kicksat/Mechanical/Avionics/Antenna Splitter/Antenna Splitter Assembly.SLDASM

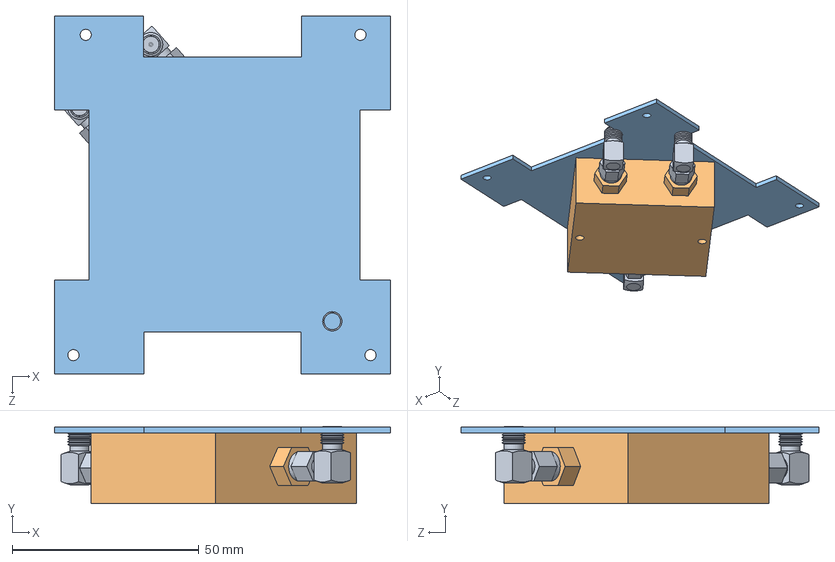
[picture p1: CAD file, 2018-08-01]
Avionics/Antenna Splitter/Antenna Splitter Assembly.SLDASM
90.0 x 20.7 x 95.9 mm
Antenna Splitter Holder
Antenna Splitter
SMA Right Angle x 3
