kicksat/Mechanical/Mechanical & Structural Components/Sprite Housing/Sprite Deployer.SLDASM

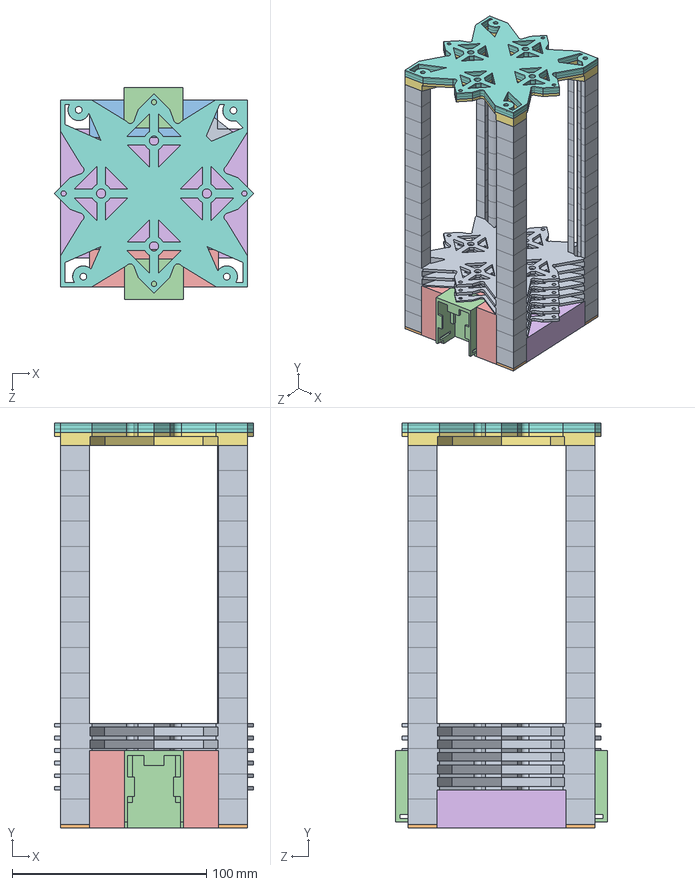
[picture p16: CAD file, 2016-09-20]
Mechanical & Structural Components/Sprite Housing/Sprite Deployer.SLDASM
102.6 x 208.4 x 109.2 mm
3dppart2 x 15
3dprintpart
BottomAntennaAttach1
Base x 2
BottomAntennaAttach2
GPSHolder
Deployer Top Part
Deployer Top Part 2 x 3
