kicksat/Mechanical/Avionics/Main Antenna/Antenna Assembly.SLDASM

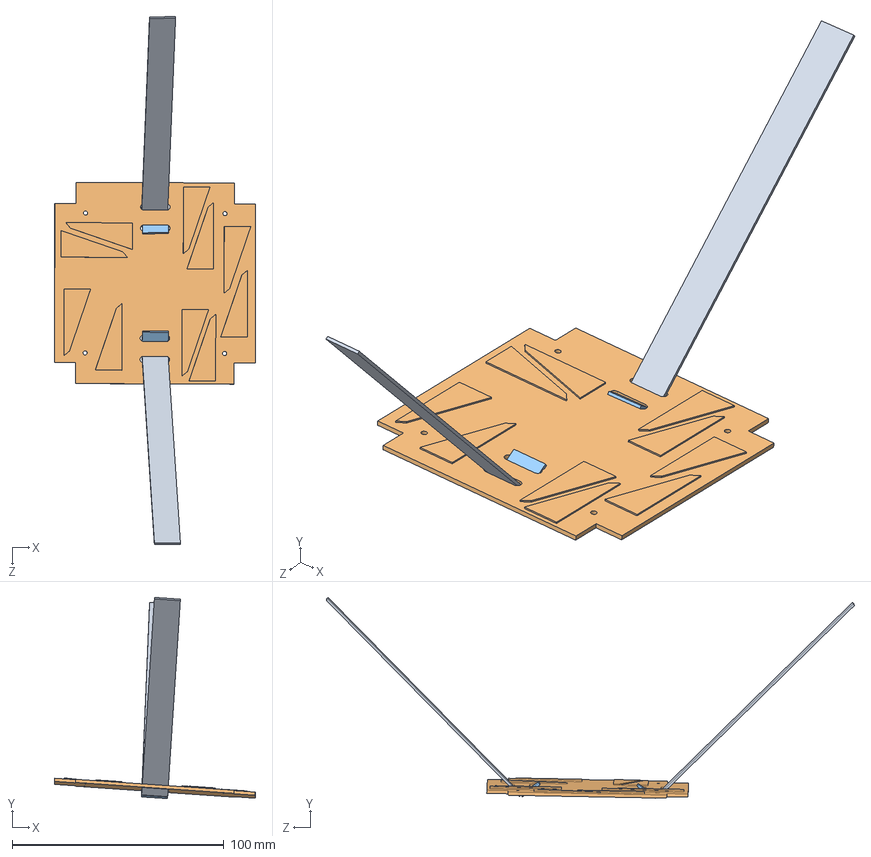
[picture p17: CAD file, 2018-08-01]
Avionics/Main Antenna/Antenna Assembly.SLDASM
95.1 x 95.0 x 249.2 mm
Antenna_Main x 2
Antenna Board
Antenna_Short x 2
