kicksat/Mechanical/Mechanical & Structural Components/Updated Deployer/UpdatedDeployerAssemblyV2.SLDASM

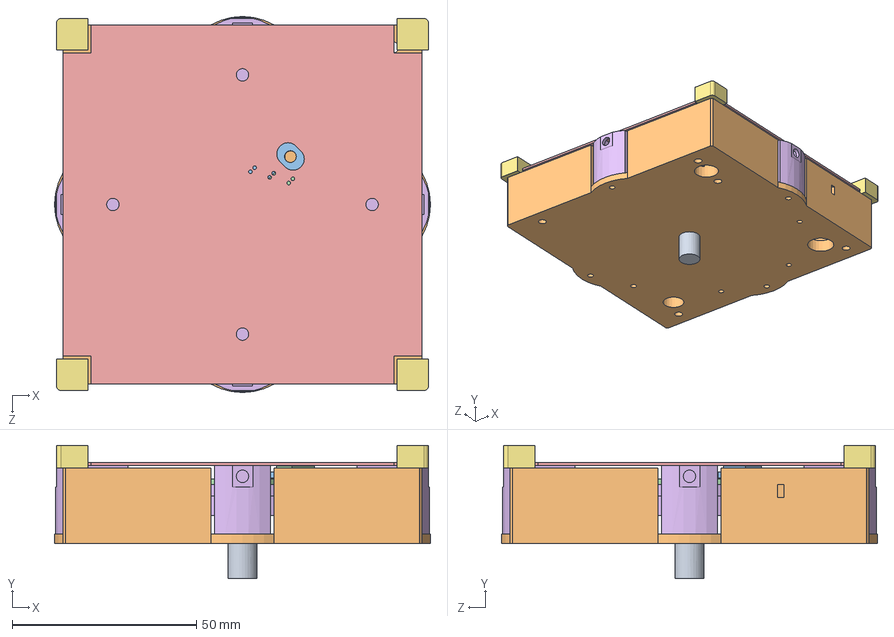
[picture p18: CAD file, 2018-09-04]
Mechanical & Structural Components/Updated Deployer/UpdatedDeployerAssemblyV2.SLDASM
102.1 x 36.2 x 102.1 mm
Bolt,8mm_x_24.6mm
DeployerBase
TopClasp
BottomClasp
CoverPlate
RetentionPlate
