kicksat/Mechanical/Mechanical & Structural Components/Sprite Deployer/Sprite Deployer.SLDASM

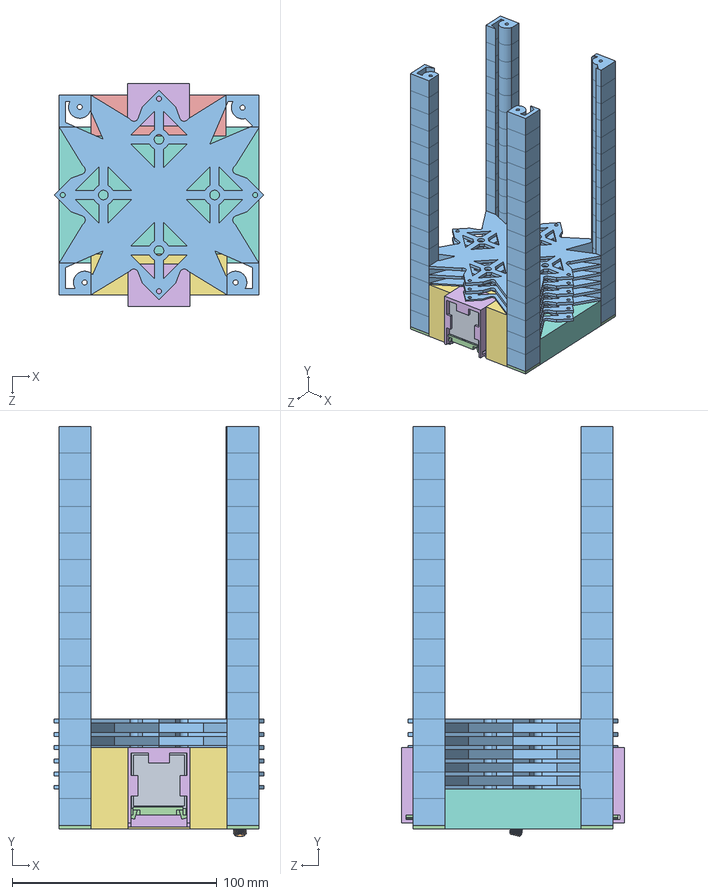
[picture p19: CAD file, 2018-08-01]
Mechanical & Structural Components/Sprite Deployer/Sprite Deployer.SLDASM
102.6 x 200.5 x 109.2 mm
3dppart2 x 15
3dprintpart
BottomAntennaAttach1
Base x 2
BottomAntennaAttach2
GPSHolder
PCB
molex 53261 x 3
FTSH-50-D
T-1S15 x 10
Micro USB
Can BMI-S-208-F
Lid BMI-S-208-F
Patch Ant GP.1575.25.4.A.02
Molex SMA 73251-1150
Led 0603 x 2
Button B3U-1000P
SMA Right Angle
GPS Antenna x 2
Slider x 2
