kicksat/Mechanical/Avionics/Batteries/M101 Battery Assembly.SLDASM

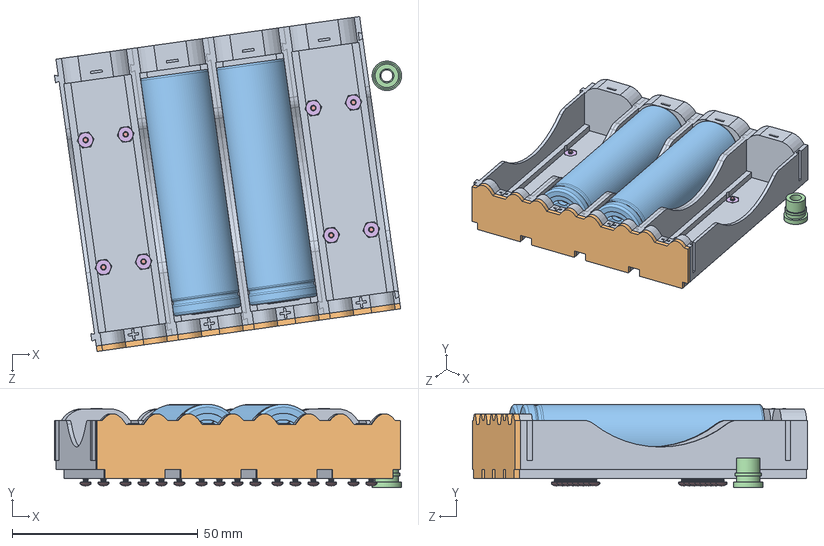
[picture p20: CAD file, 2018-08-30]
Avionics/Batteries/M101 Battery Assembly.SLDASM
93.5 x 22.5 x 90.2 mm
single battery holder x 4
battery pack cap
Battery, 18650_LGABC11865_3.7V x 2
grommet, 1-8in ID, 5269T211
screw, pan head, 0-80, 1_8L, 316SS, 91400A030 x 16
nut, 0-80, standard, 18-8SS, 91841A115 x 16
