kicksat/Mechanical/Mechanical & Structural Components/Sprite Deployer/BottomStart.SLDASM

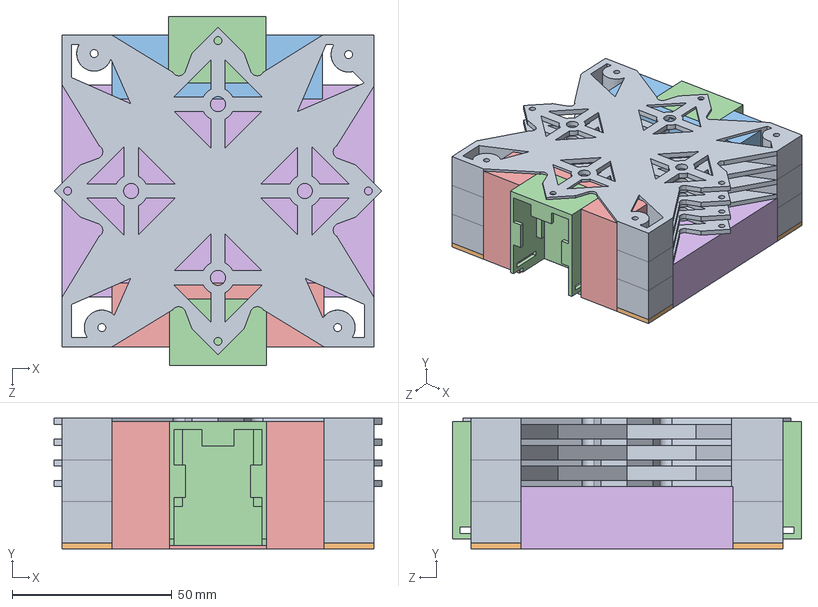
[picture p21: CAD file, 2018-08-01]
Mechanical & Structural Components/Sprite Deployer/BottomStart.SLDASM
102.6 x 40.9 x 109.2 mm
3dppart2 x 3
3dprintpart
BottomAntennaAttach1
Base x 2
BottomAntennaAttach2
GPSHolder
