kicksat/Mechanical/Avionics/GPS/piksi_v2_3_cad/FTSH-105-01-X-D-K.SLDASM

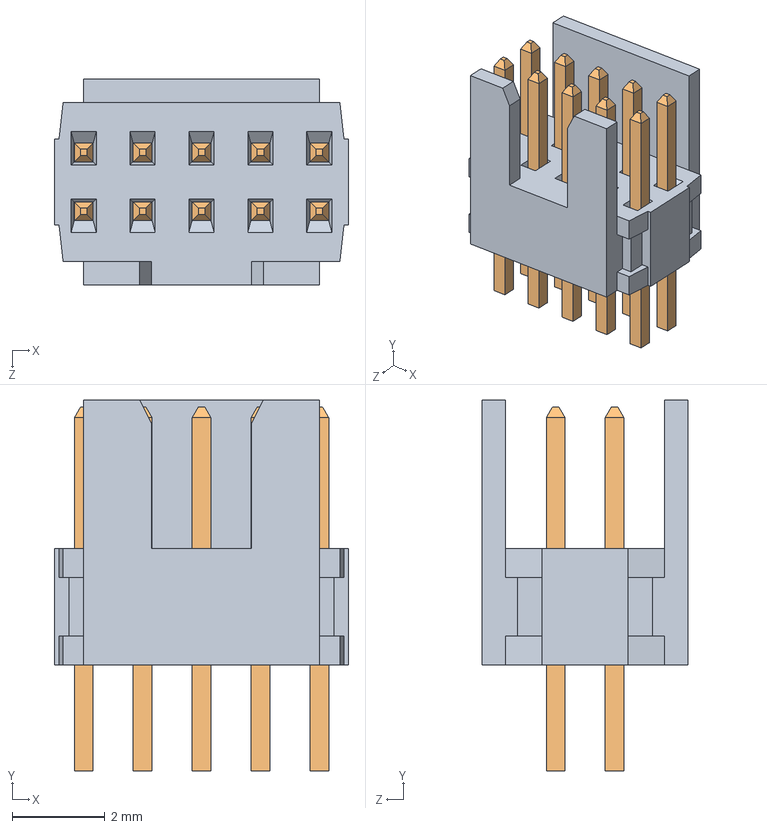
[picture p23: CAD file, 2018-08-01]
Avionics/GPS/piksi_v2_3_cad/FTSH-105-01-X-D-K.SLDASM
6.35 x 8.00 x 4.45 mm
FTSH-50-D
T-1S15 x 10
