kicksat/Mechanical/Avionics/GPS/piksi_v2_3_cad/BMI-S-208-F.SLDASM

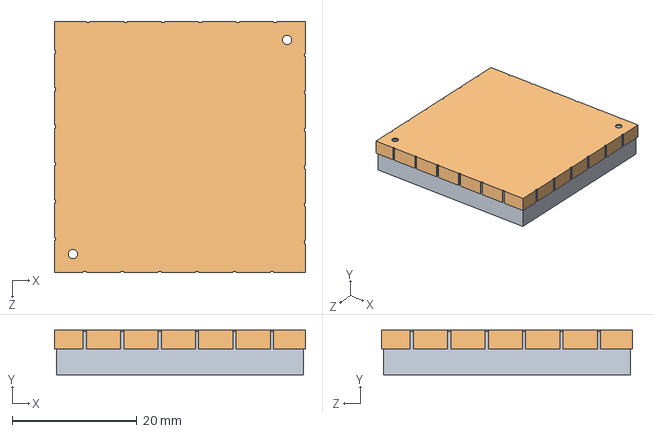
[picture p24: CAD file, 2018-08-01]
Avionics/GPS/piksi_v2_3_cad/BMI-S-208-F.SLDASM
40.2 x 7.20 x 40.2 mm
Can BMI-S-208-F
Lid BMI-S-208-F
