kicksat/Mechanical/Avionics/GPS/piksi_v2_3_cad/swiftnav_v2_3.SLDASM

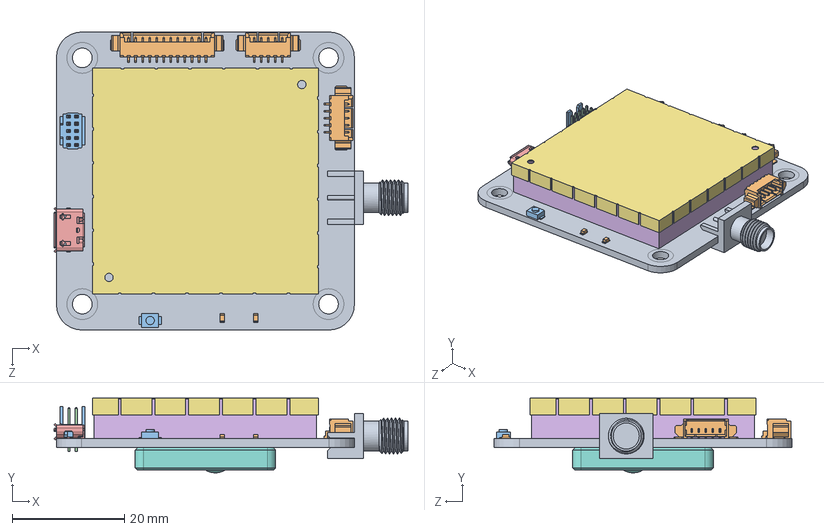
[picture p25: CAD file, 2015-09-18]
Avionics/GPS/piksi_v2_3_cad/swiftnav_v2_3.SLDASM
63.0 x 13.3 x 53.0 mm
PCB
molex 53261 x 3
FTSH-50-D
T-1S15 x 10
Micro USB
Can BMI-S-208-F
Lid BMI-S-208-F
Patch Ant GP.1575.25.4.A.02
Molex SMA 73251-1150
Led 0603 x 2
Button B3U-1000P
