kicksat/Mechanical/Avionics/Batteries/grommet, 1-8in ID, 5269T211.SLDPRT

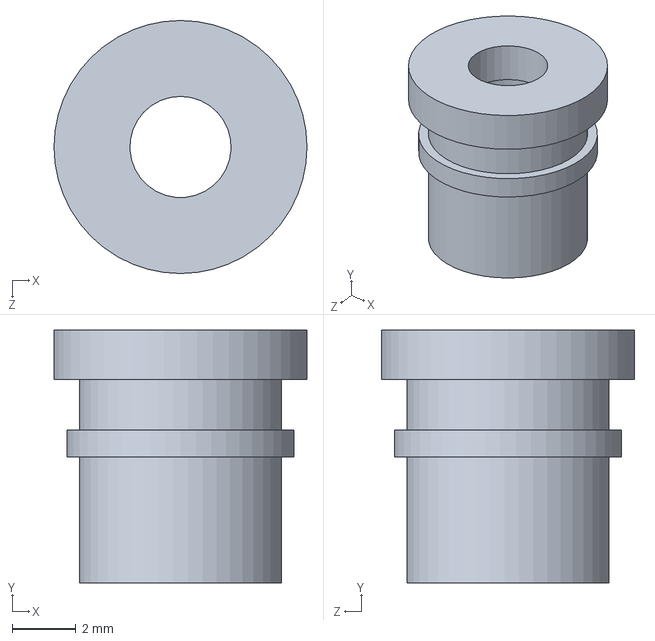
[picture p26: CAD file, 2018-08-30]
Avionics/Batteries/grommet, 1-8in ID, 5269T211.SLDPRT
7.94 x 7.94 x 7.94 mm
