kicksat/Mechanical/Avionics/Flight Computer and Radio Board/Connector1.SLDPRT

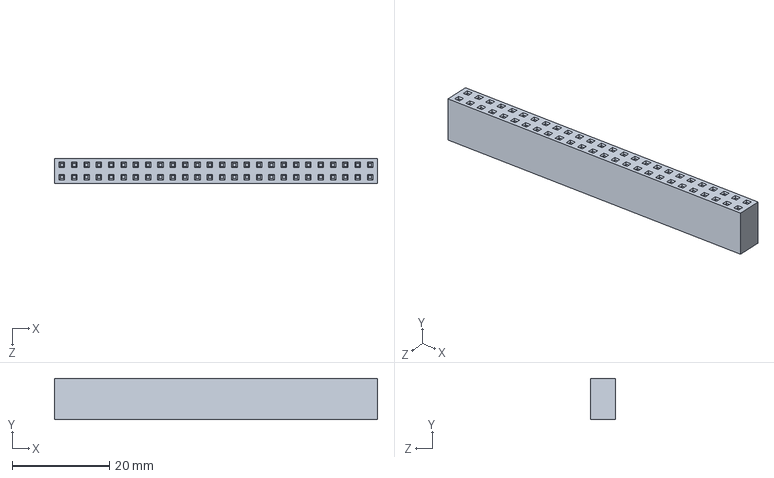
[picture p27: CAD file, 2018-08-01]
Avionics/Flight Computer and Radio Board/Connector1.SLDPRT
66.5 x 8.51 x 5.08 mm
