kicksat/Mechanical/Avionics/GPS/GPS Antenna.SLDPRT

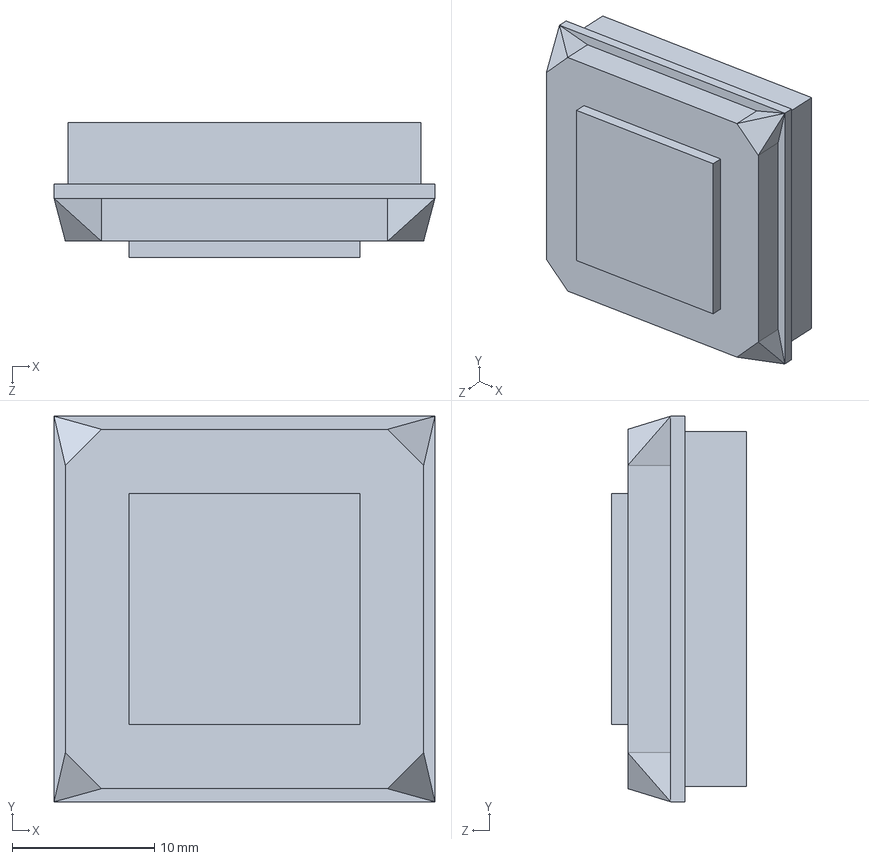
[picture p28: CAD file, 2018-08-01]
Avionics/GPS/GPS Antenna.SLDPRT
26.8 x 27.2 x 9.50 mm
