kicksat/Mechanical/Avionics/GPS/piksi_v2_3_cad/molex 53261.SLDPRT

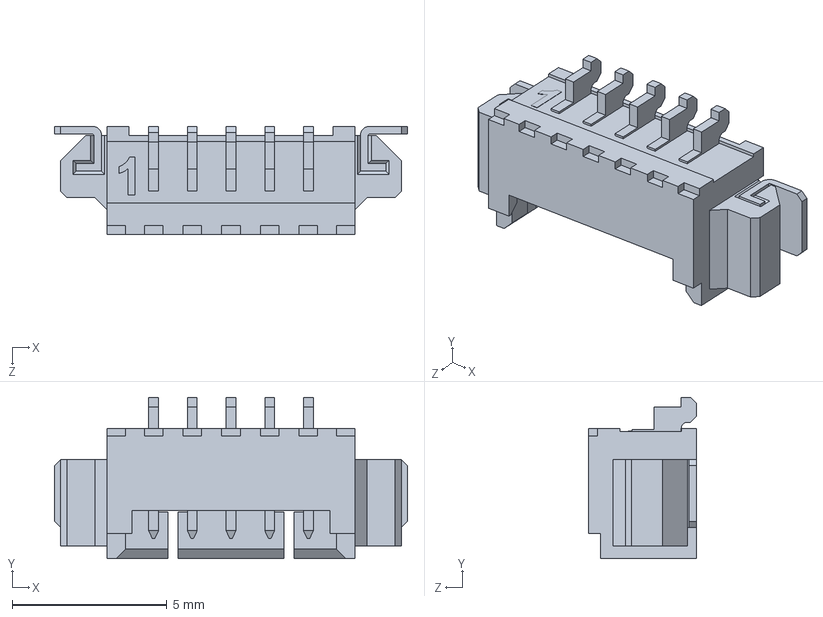
[picture p29: CAD file, 2018-08-01]
Avionics/GPS/piksi_v2_3_cad/molex 53261.SLDPRT
11.4 x 5.20 x 3.50 mm
