kicksat/Mechanical/Avionics/Main Antenna/Antenna Board.SLDPRT

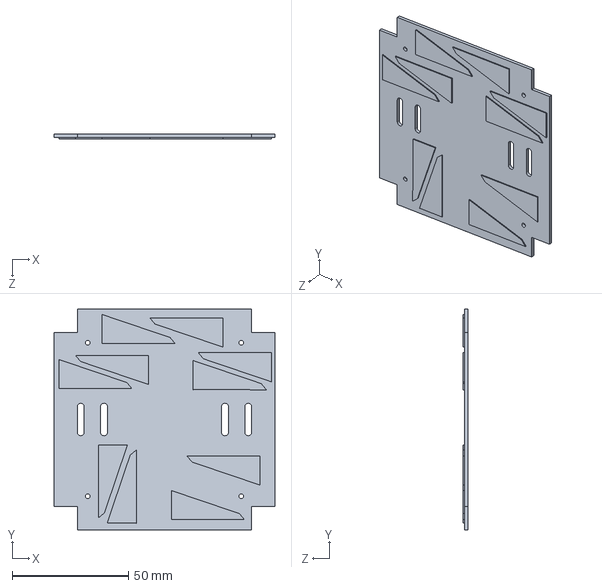
[picture p30: CAD file, 2018-08-01]
Avionics/Main Antenna/Antenna Board.SLDPRT
95.0 x 95.0 x 2.00 mm
