kicksat/Mechanical/Avionics/Polarized Connectors.SLDPRT

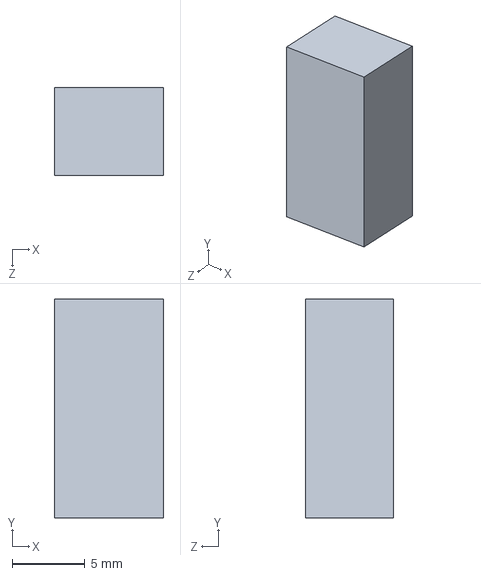
[picture p31: CAD file, 2015-09-25]
Avionics/Polarized Connectors.SLDPRT
7.50 x 15.0 x 6.00 mm
