kicksat/Mechanical/Mechanical & Structural Components/Outershell/Outershell.SLDPRT

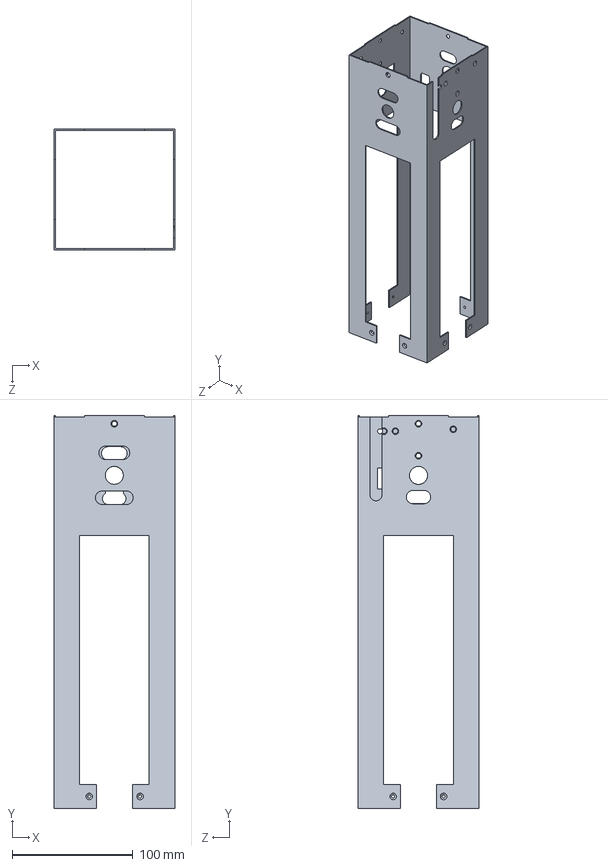
[picture p32: CAD file, 2018-08-01]
Mechanical & Structural Components/Outershell/Outershell.SLDPRT
100.0 x 325.3 x 100.0 mm
