kicksat/Mechanical/Mechanical & Structural Components/Sprite Housing/Slider.SLDPRT

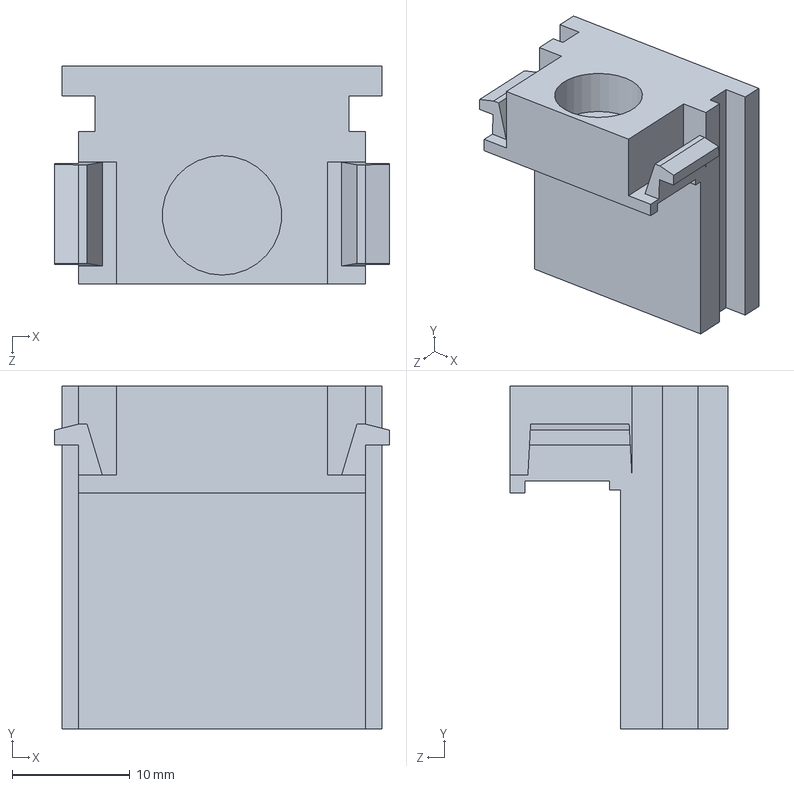
[picture p33: CAD file, 2016-11-20]
Mechanical & Structural Components/Sprite Housing/Slider.SLDPRT
28.5 x 29.1 x 18.5 mm
