kicksat/Mechanical/Mechanical & Structural Components/Top and Deployer/CarbonFiberRodX.SLDPRT

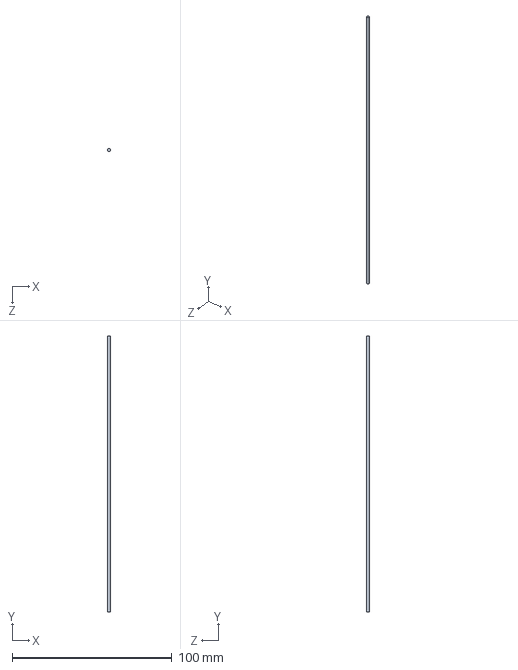
[picture p34: CAD file, 2018-08-01]
Mechanical & Structural Components/Top and Deployer/CarbonFiberRodX.SLDPRT
1.90 x 173.0 x 1.90 mm
