kicksat/Mechanical/Mechanical & Structural Components/Top and Deployer/mnc27/DeployerPiece#1_v5.STL

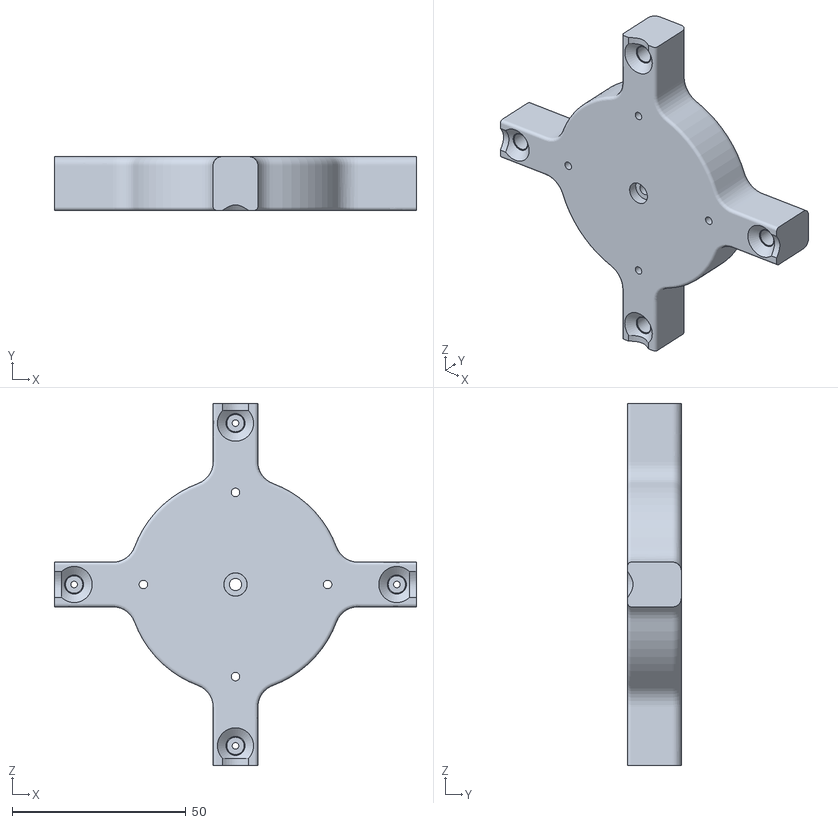
[picture p35: CAD file, 2016-10-16]
Mechanical & Structural Components/Top and Deployer/mnc27/DeployerPiece#1_v5.STL
104.2 x 15.4 x 104.2
