kicksat/Mechanical/Mechanical & Structural Components/Updated Deployer/Body1.sldprt

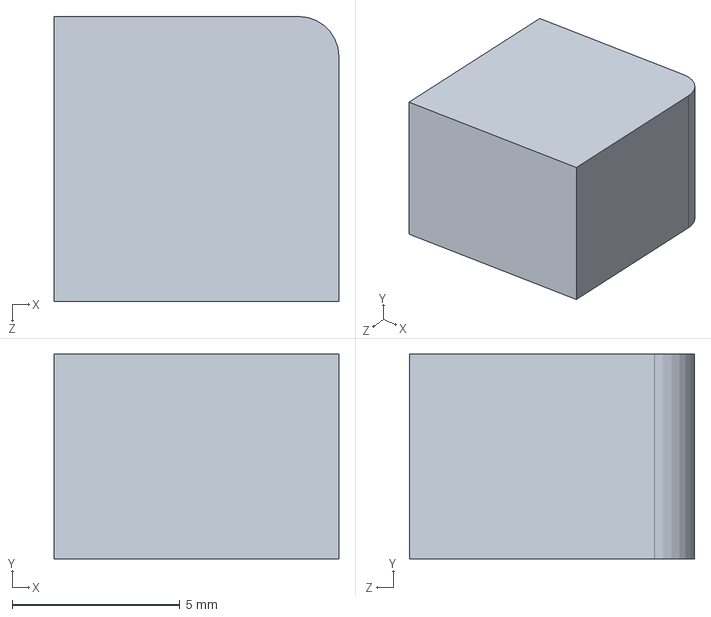
[picture p36: CAD file, 2018-09-04]
Mechanical & Structural Components/Updated Deployer/Body1.sldprt
8.50 x 6.10 x 8.50 mm
