kicksat/Mechanical/Avionics/Antenna Splitter/Antenna Splitter.SLDPRT

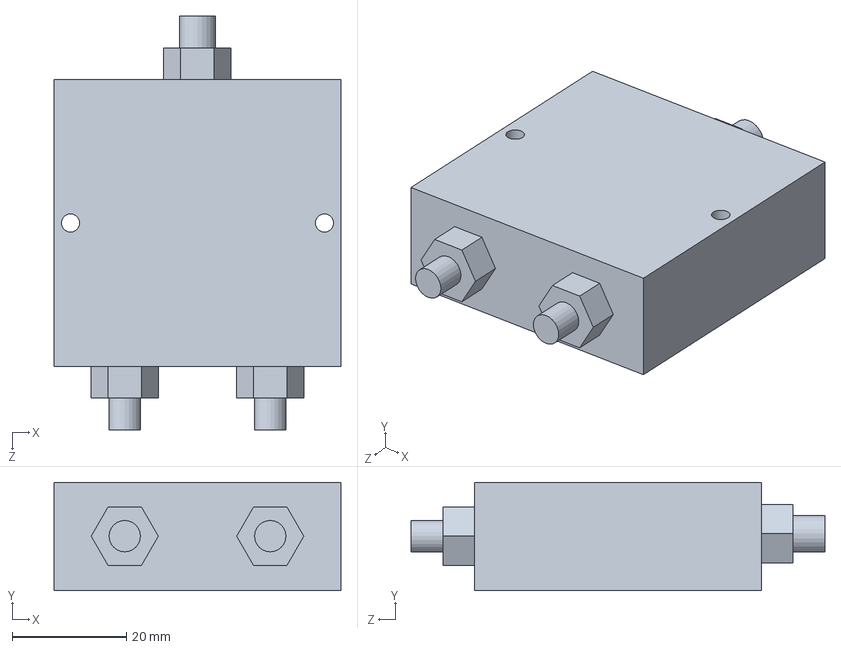
[picture p37: CAD file, 2018-08-01]
Avionics/Antenna Splitter/Antenna Splitter.SLDPRT
50.3 x 19.0 x 72.5 mm
