kicksat/Mechanical/Avionics/Batteries/single battery holder.SLDPRT

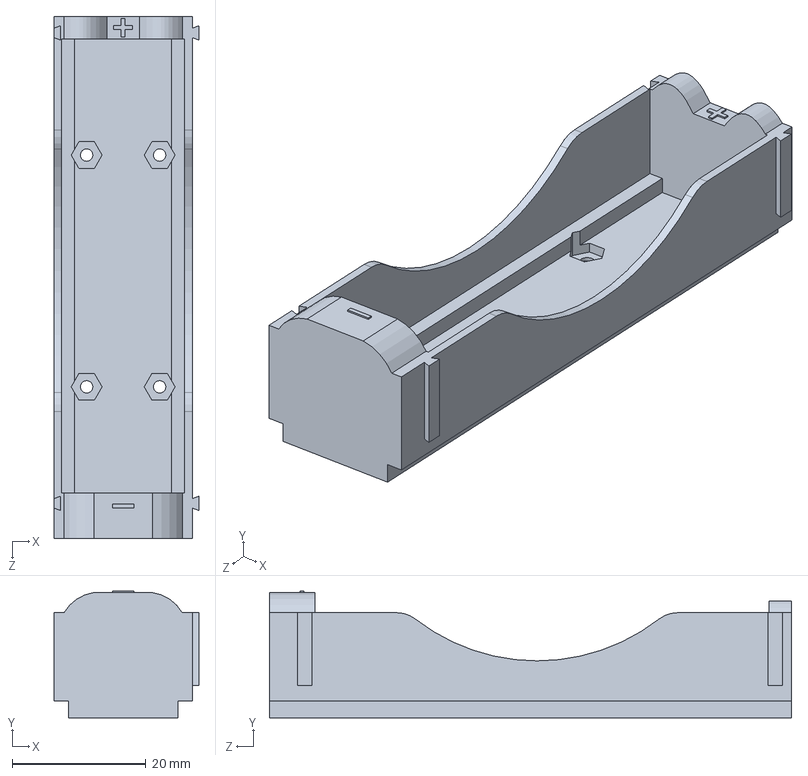
[picture p38: CAD file, 2018-08-30]
Avionics/Batteries/single battery holder.SLDPRT
21.7 x 18.9 x 78.0 mm
