kicksat/Mechanical/Avionics/Flight Computer and Radio Board/CircuitBoardPart.SLDPRT

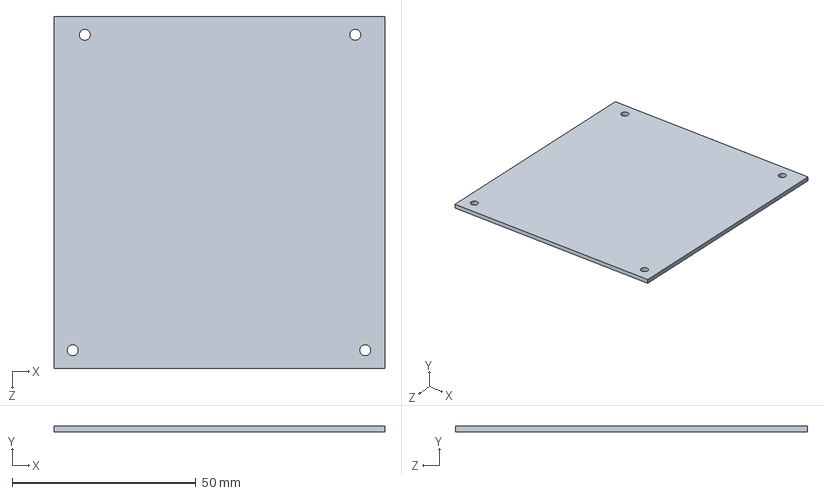
[picture p39: CAD file, 2018-08-01]
Avionics/Flight Computer and Radio Board/CircuitBoardPart.SLDPRT
90.0 x 1.60 x 95.9 mm
