kicksat/Mechanical/Avionics/GPS/piksi_v2_3_cad/PCB.SLDPRT

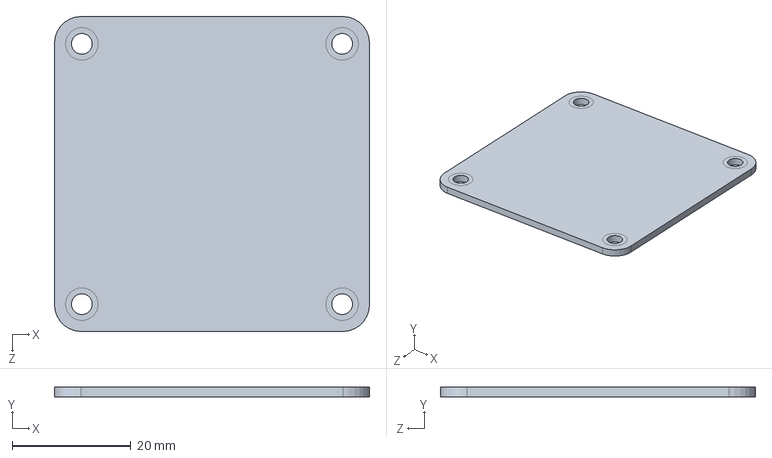
[picture p40: CAD file, 2018-08-01]
Avionics/GPS/piksi_v2_3_cad/PCB.SLDPRT
53.0 x 1.61 x 53.0 mm
