kicksat/Mechanical/Avionics/GPS/SMA Right Angle.SLDPRT

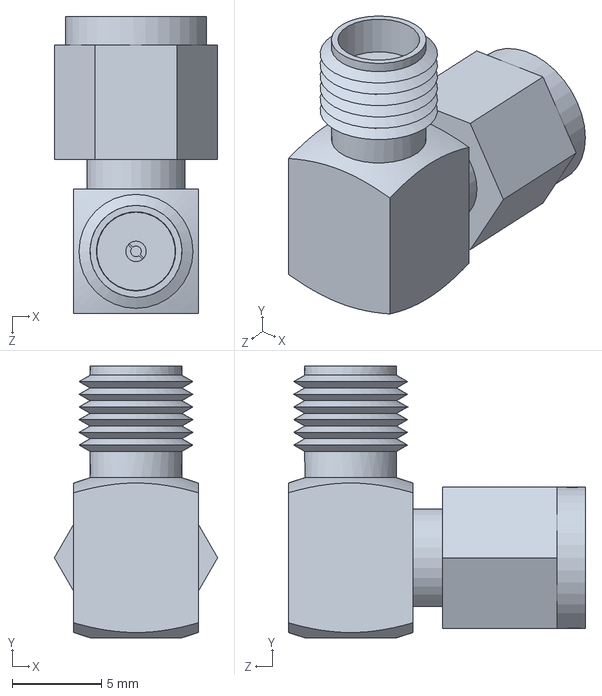
[picture p41: CAD file, 2018-08-01]
Avionics/GPS/SMA Right Angle.SLDPRT
9.15 x 15.2 x 16.7 mm
