kicksat/Mechanical/Mechanical & Structural Components/Sprite Deployer/Slider.SLDPRT

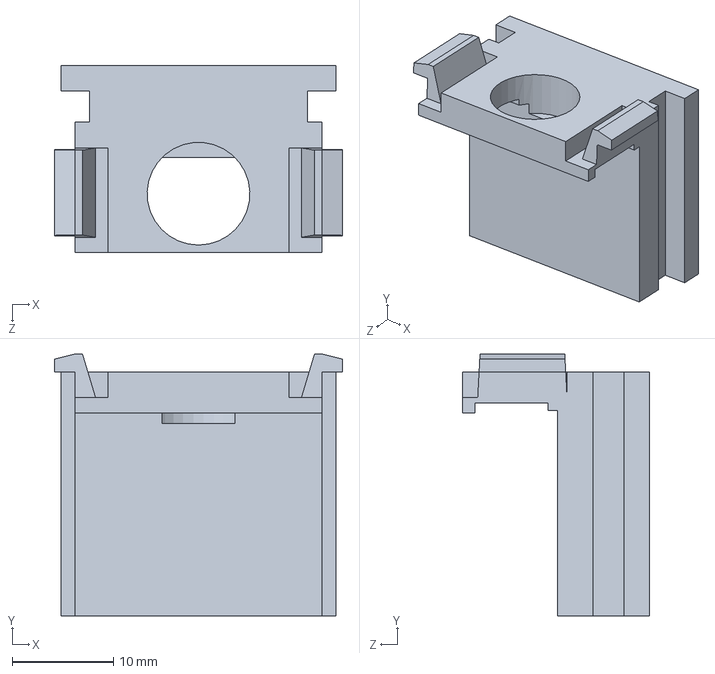
[picture p42: CAD file, 2018-08-01]
Mechanical & Structural Components/Sprite Deployer/Slider.SLDPRT
28.5 x 25.9 x 18.5 mm
