kicksat/Mechanical/Avionics/Antenna Splitter/Antenna Splitter Holder.SLDPRT

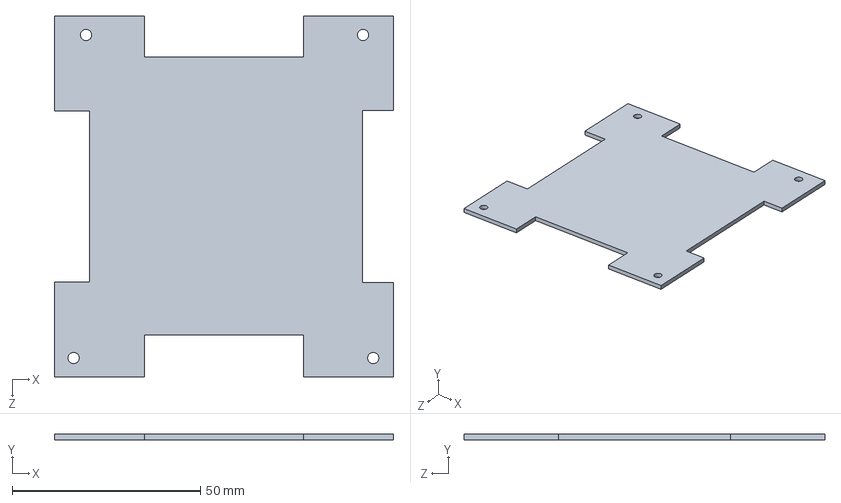
[picture p43: CAD file, 2018-08-01]
Avionics/Antenna Splitter/Antenna Splitter Holder.SLDPRT
90.0 x 1.60 x 95.9 mm
