kicksat/Mechanical/Avionics/GPS/piksi_v2_3_cad/Micro USB.SLDPRT

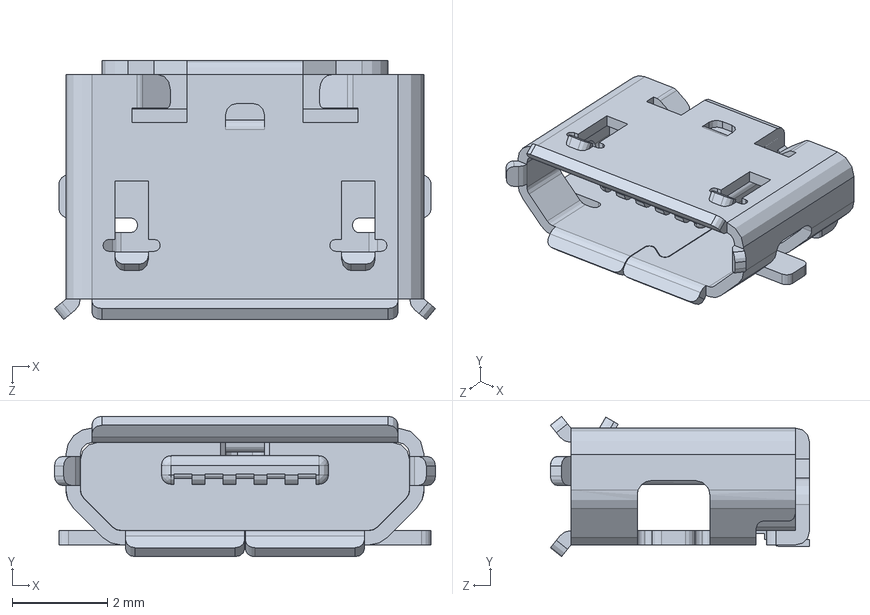
[picture p44: CAD file, 2018-08-01]
Avionics/GPS/piksi_v2_3_cad/Micro USB.SLDPRT
7.98 x 2.94 x 5.43 mm
