kicksat/Mechanical/Avionics/Main Antenna/Antenna_Short.SLDPRT

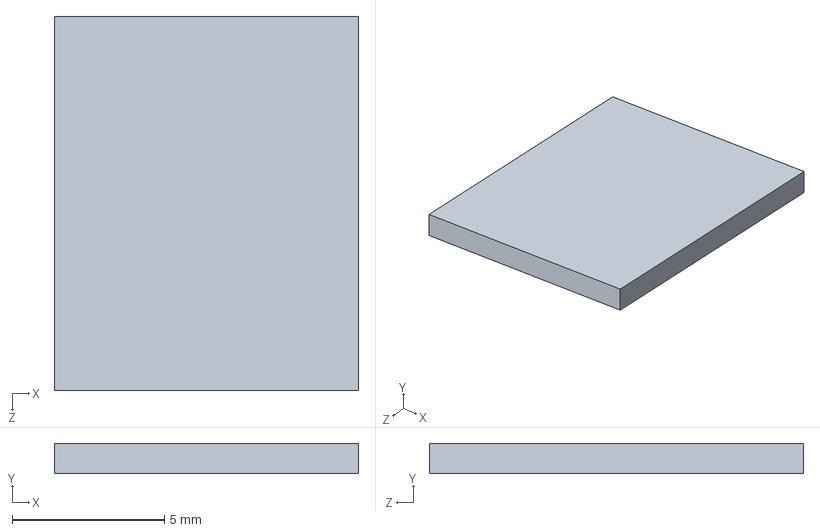
[picture p45: CAD file, 2018-08-01]
Avionics/Main Antenna/Antenna_Short.SLDPRT
10.0 x 1.00 x 12.3 mm
