kicksat/Mechanical/Mechanical & Structural Components/Bottom/RollerDeployerSwitch.SLDPRT

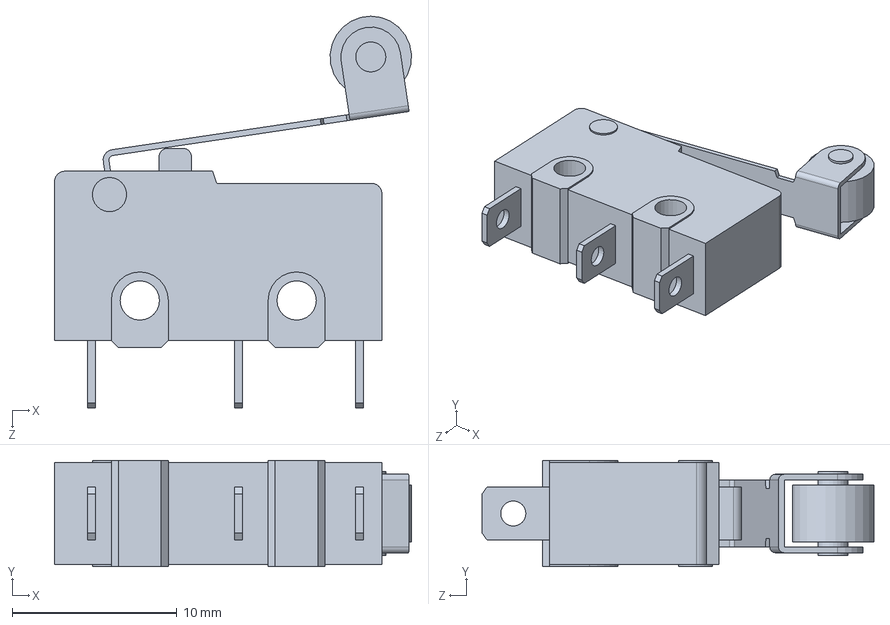
[picture p46: CAD file, 2018-08-01]
Mechanical & Structural Components/Bottom/RollerDeployerSwitch.SLDPRT
21.7 x 6.44 x 23.8 mm
