kicksat/Mechanical/Mechanical & Structural Components/Sprite Deployer/3dprintpart.SLDPRT

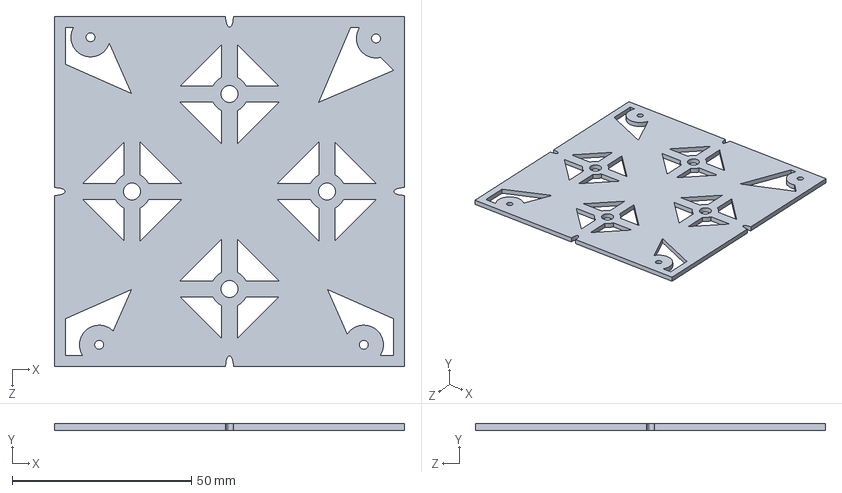
[picture p47: CAD file, 2018-08-01]
Mechanical & Structural Components/Sprite Deployer/3dprintpart.SLDPRT
97.6 x 1.85 x 97.6 mm
