kicksat/Mechanical/Mechanical & Structural Components/Top and Deployer/DeployerPiece#1_v5.SLDPRT

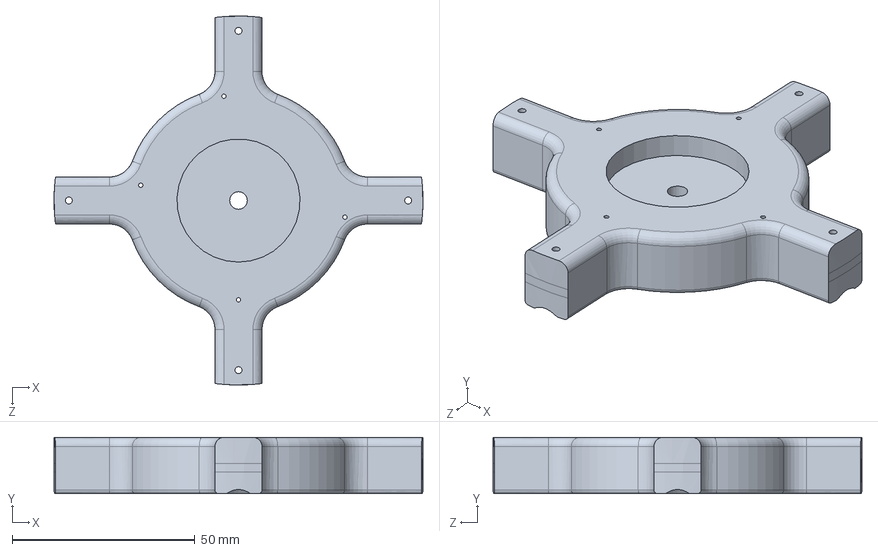
[picture p48: CAD file, 2018-08-01]
Mechanical & Structural Components/Top and Deployer/DeployerPiece#1_v5.SLDPRT
101.0 x 15.4 x 101.0 mm
