kicksat/Mechanical/Mechanical & Structural Components/Updated Deployer/TeeNut.SLDPRT

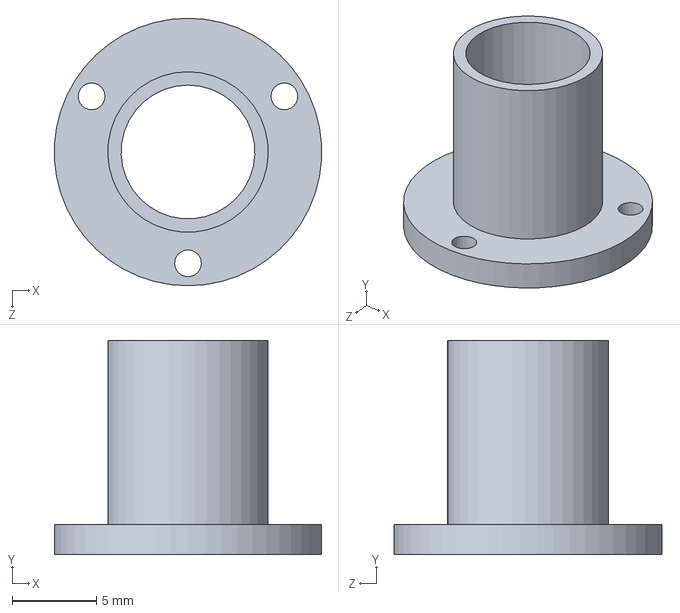
[picture p49: CAD file, 2018-09-04]
Mechanical & Structural Components/Updated Deployer/TeeNut.SLDPRT
15.8 x 12.7 x 15.9 mm
