kicksat/Mechanical/Avionics/Batteries/nut, 0-80, standard, 18-8SS, 91841A115.SLDPRT

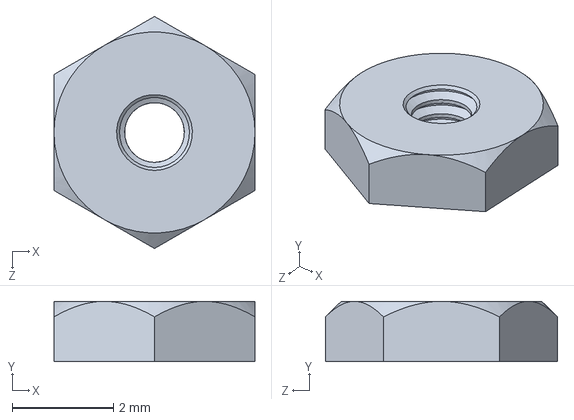
[picture p50: CAD file, 2018-08-30]
Avionics/Batteries/nut, 0-80, standard, 18-8SS, 91841A115.SLDPRT
3.97 x 1.19 x 4.58 mm
