kicksat/Mechanical/Avionics/GPS/piksi_v2_3_cad/FTSH-50-D.sldprt

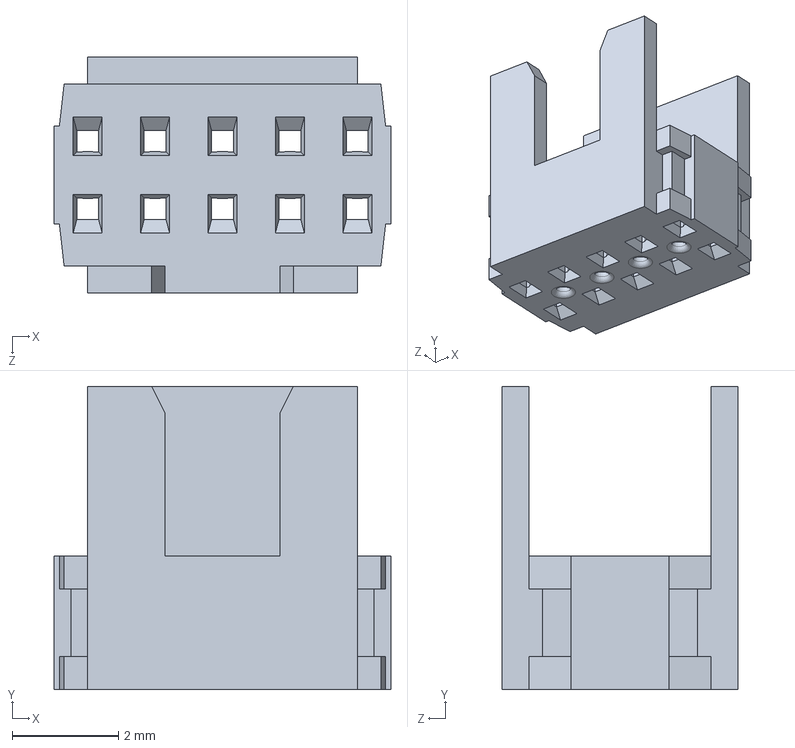
[picture p51: CAD file, 2018-08-01]
Avionics/GPS/piksi_v2_3_cad/FTSH-50-D.sldprt
6.35 x 5.72 x 4.45 mm
