kicksat/Mechanical/Avionics/Solar Panels/Side X Solar Cells.SLDPRT

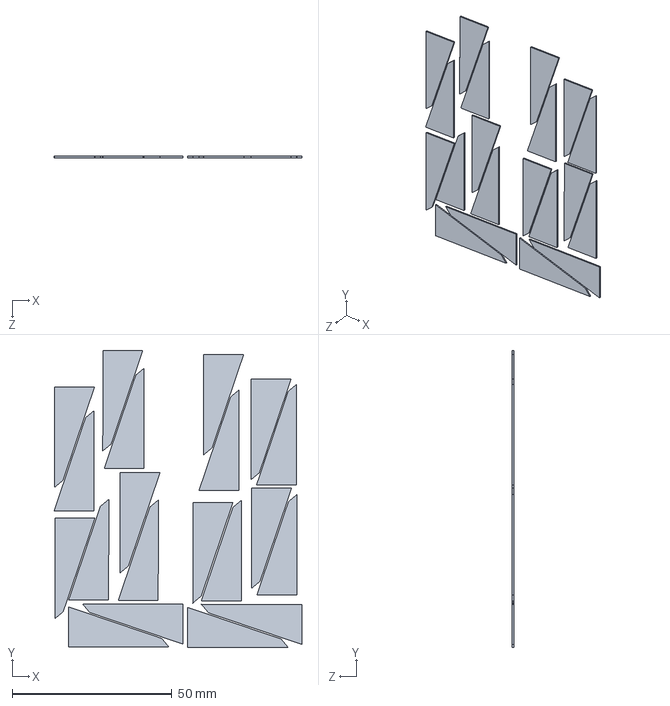
[picture p52: CAD file, 2018-08-01]
Avionics/Solar Panels/Side X Solar Cells.SLDPRT
77.6 x 93.0 x 0.5 mm
