kicksat/Mechanical/Mechanical & Structural Components/Bottom/DeployerSwitchPlunger.SLDPRT

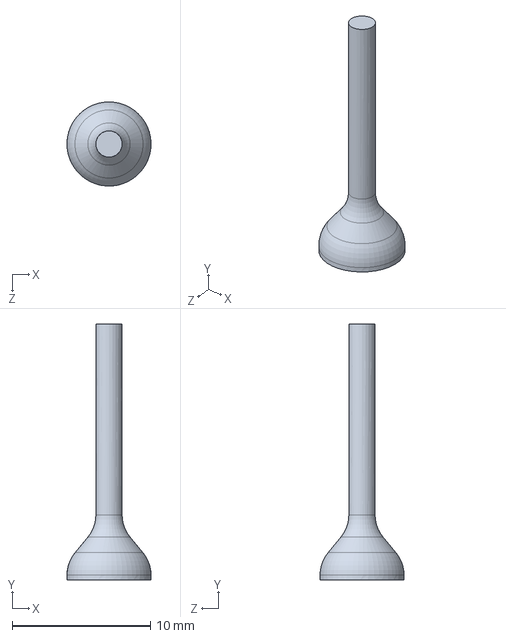
[picture p53: CAD file, 2015-09-18]
Mechanical & Structural Components/Bottom/DeployerSwitchPlunger.SLDPRT
6.09 x 18.5 x 6.10 mm
