kicksat/Mechanical/Mechanical & Structural Components/Sprite Deployer/3dppart2.SLDPRT

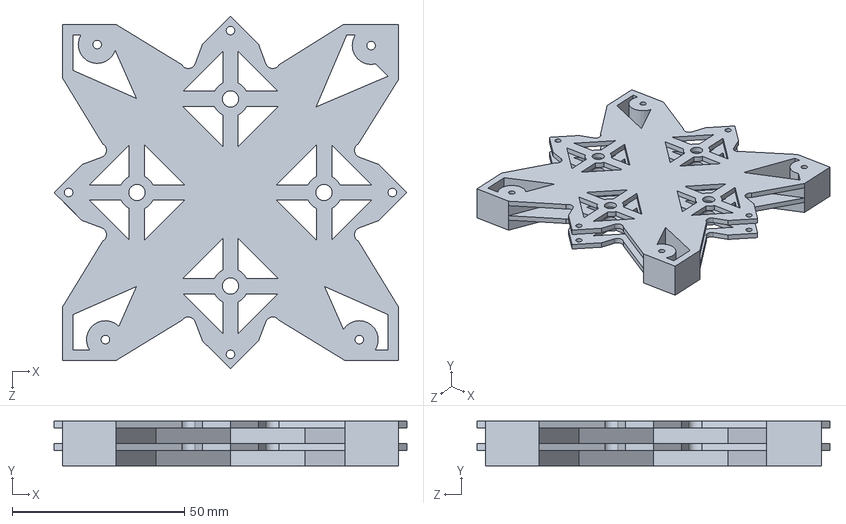
[picture p54: CAD file, 2018-08-01]
Mechanical & Structural Components/Sprite Deployer/3dppart2.SLDPRT
102.6 x 13.0 x 102.6 mm
