kicksat/Mechanical/Mechanical & Structural Components/Sprite Housing/SpriteMajorDimensions.STEP

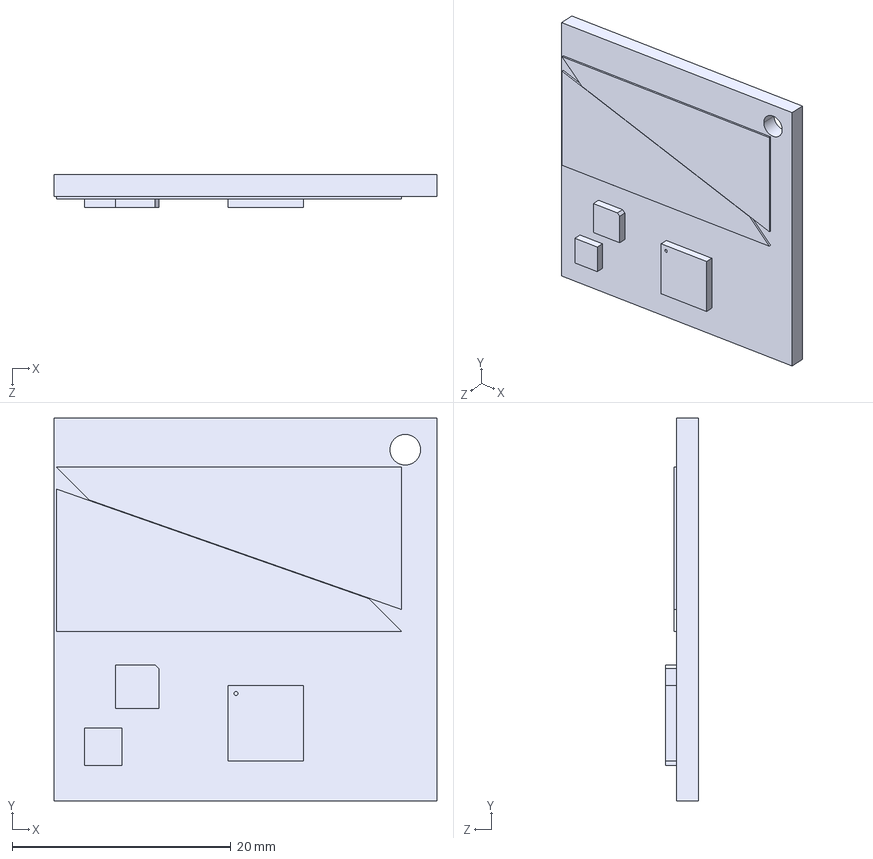
[picture p55: CAD file, 2016-04-13]
Mechanical & Structural Components/Sprite Housing/SpriteMajorDimensions.STEP
35.0 x 35.0 x 3.00 mm
