kicksat/Mechanical/Mechanical & Structural Components/Top and Deployer/Top.SLDPRT

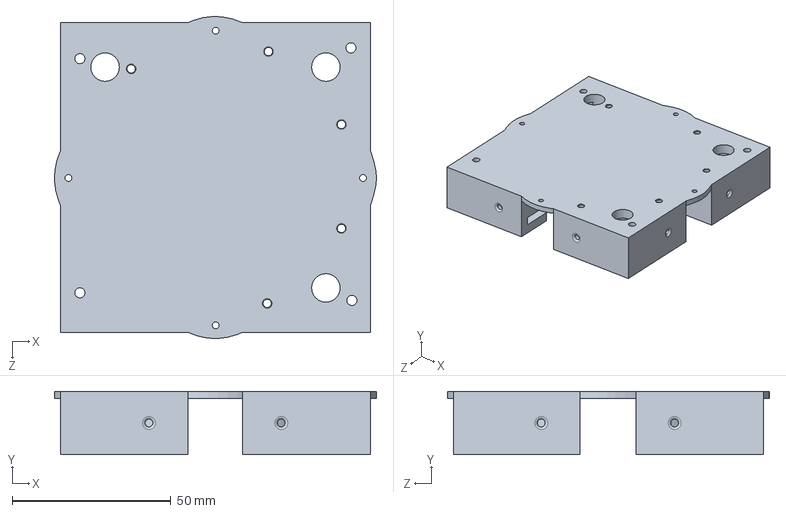
[picture p56: CAD file, 2018-08-01]
Mechanical & Structural Components/Top and Deployer/Top.SLDPRT
101.5 x 19.9 x 101.5 mm
