kicksat/Mechanical/Avionics/GPS/piksi_v2_3_cad/Button B3U-1000P.SLDPRT

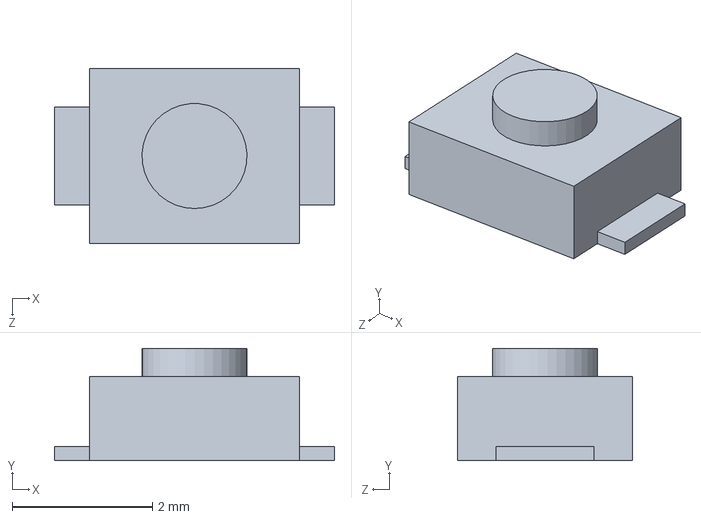
[picture p57: CAD file, 2018-08-01]
Avionics/GPS/piksi_v2_3_cad/Button B3U-1000P.SLDPRT
4.00 x 1.60 x 2.50 mm
