kicksat/Mechanical/Avionics/Main Antenna/Antenna Board 2.SLDPRT

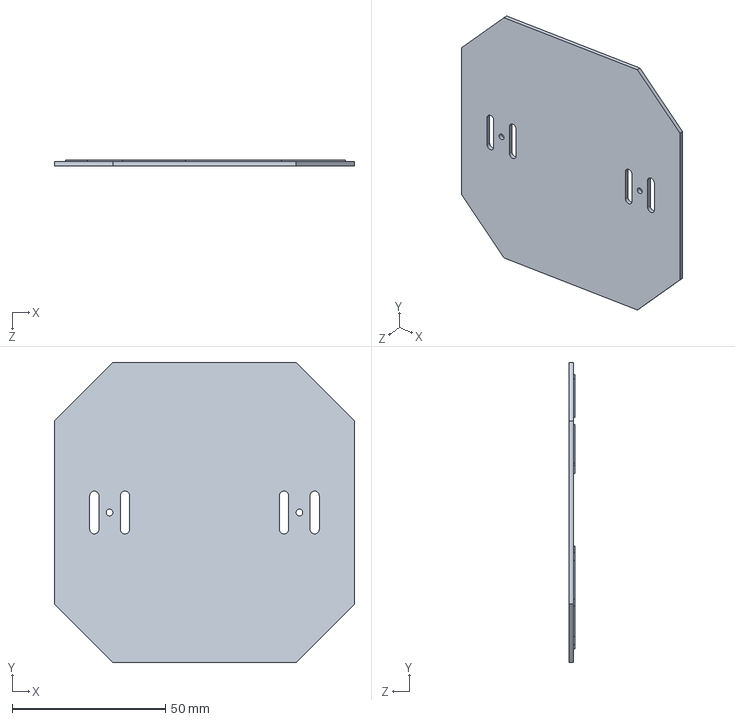
[picture p58: CAD file, 2015-09-25]
Avionics/Main Antenna/Antenna Board 2.SLDPRT
98.0 x 98.0 x 2.00 mm
