kicksat/Mechanical/Avionics/Solar Panels/Side Y Solar Panel.SLDPRT

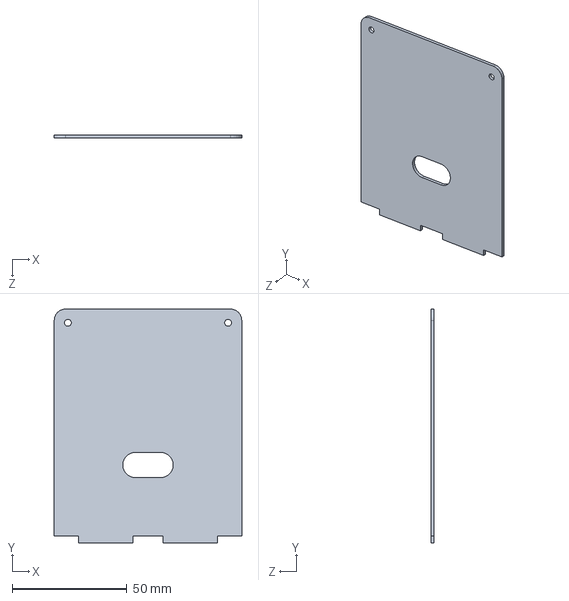
[picture p59: CAD file, 2018-08-01]
Avionics/Solar Panels/Side Y Solar Panel.SLDPRT
81.8 x 102.0 x 1.50 mm
