kicksat/Mechanical/Mechanical & Structural Components/Bottom/DeployerSwitchExtensionAssem.SLDPRT

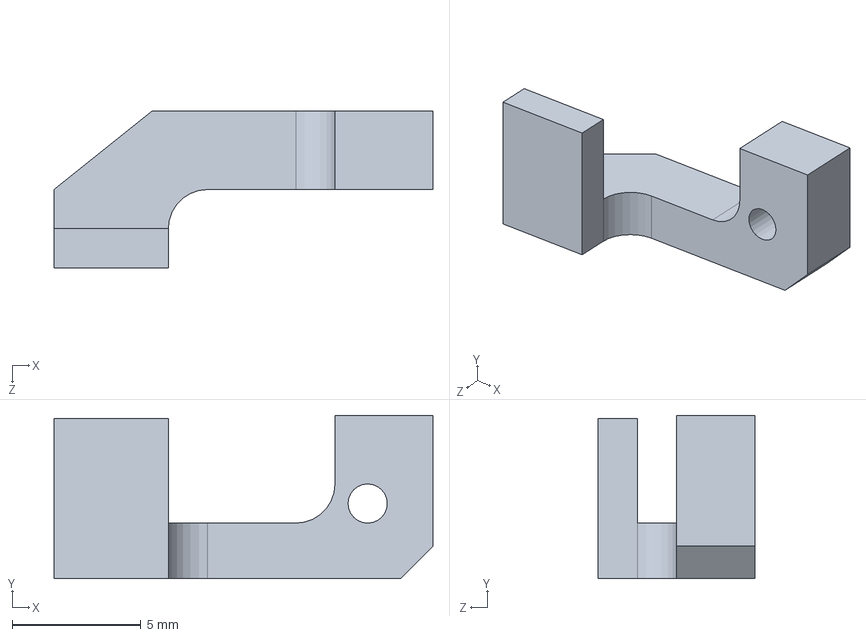
[picture p60: CAD file, 2015-09-18]
Mechanical & Structural Components/Bottom/DeployerSwitchExtensionAssem.SLDPRT
14.7 x 6.35 x 6.10 mm
