kicksat/Mechanical/Mechanical & Structural Components/Sprite Deployer/5pinConnector.SLDPRT

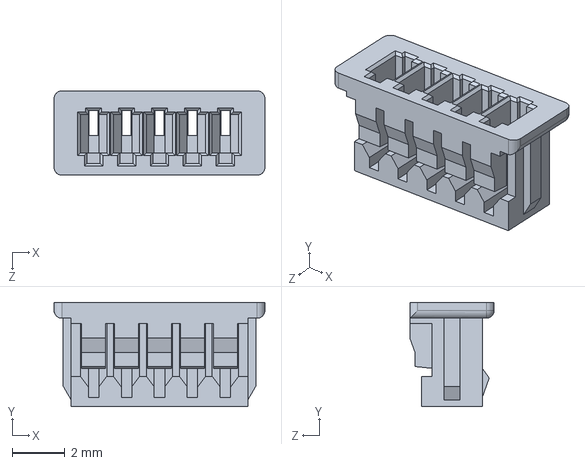
[picture p61: CAD file, 2018-08-01]
Mechanical & Structural Components/Sprite Deployer/5pinConnector.SLDPRT
8.00 x 3.95 x 3.20 mm
