kicksat/Mechanical/Mechanical & Structural Components/Top and Deployer/Leg(Top).SLDPRT

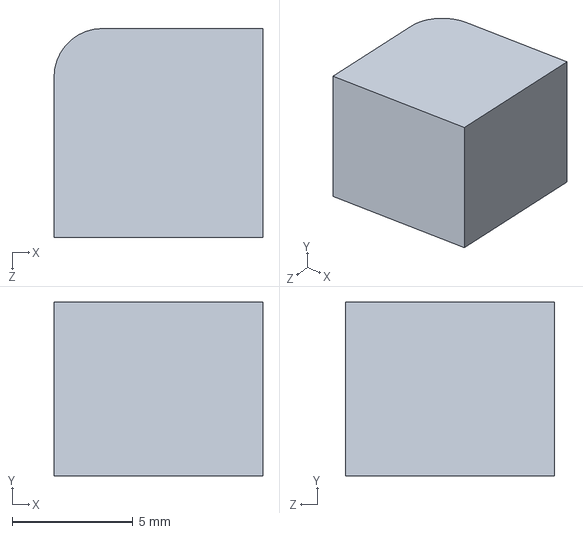
[picture p62: CAD file, 2018-08-01]
Mechanical & Structural Components/Top and Deployer/Leg(Top).SLDPRT
8.65 x 7.20 x 8.65 mm
