kicksat/Mechanical/Mechanical & Structural Components/Updated Deployer/DeployerBase.SLDPRT

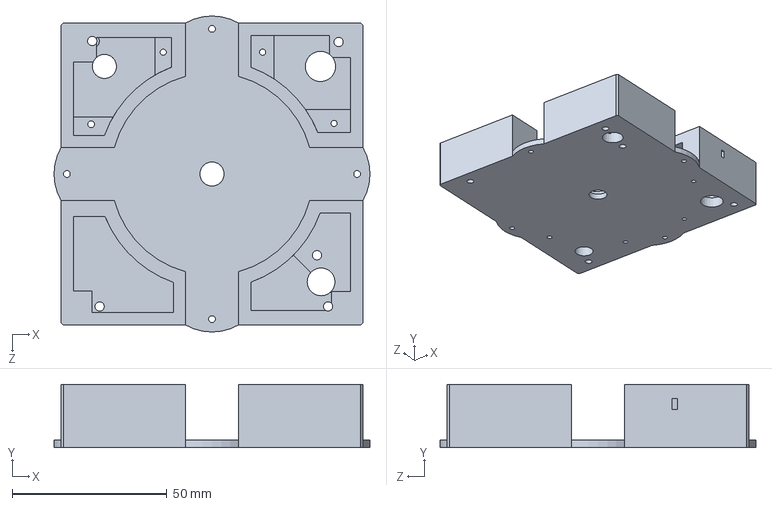
[picture p63: CAD file, 2018-09-04]
Mechanical & Structural Components/Updated Deployer/DeployerBase.SLDPRT
102.1 x 20.5 x 102.1 mm
