kicksat/Mechanical/Avionics/Batteries/Battery, 18650_LGABC11865_3.7V.sldprt

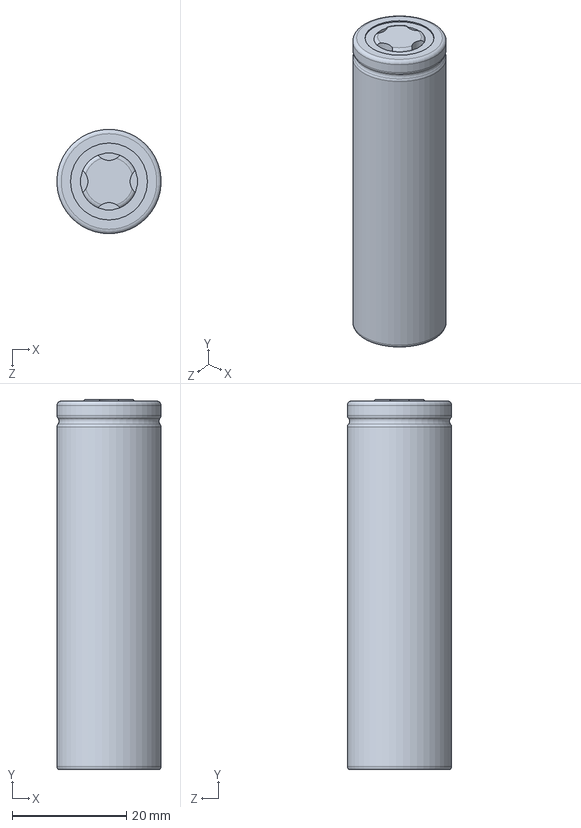
[picture p64: CAD file, 2018-08-30]
Avionics/Batteries/Battery, 18650_LGABC11865_3.7V.sldprt
18.3 x 64.9 x 18.3 mm
