kicksat/Mechanical/Avionics/GPS/piksi_v2_3_cad/Lid BMI-S-208-F.SLDPRT

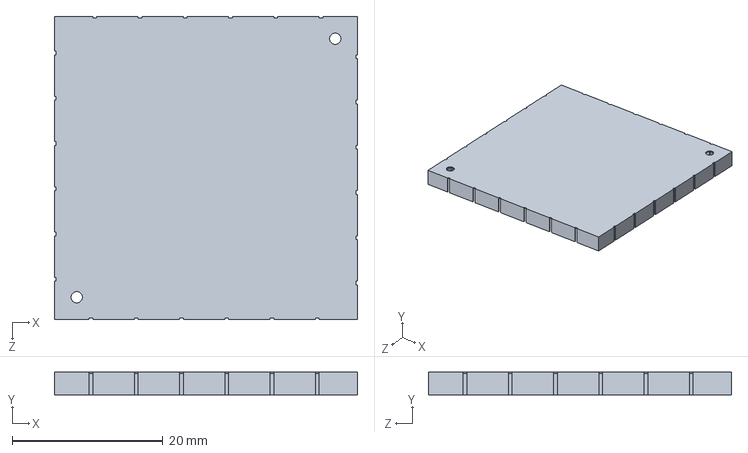
[picture p65: CAD file, 2018-08-01]
Avionics/GPS/piksi_v2_3_cad/Lid BMI-S-208-F.SLDPRT
40.2 x 3.00 x 40.2 mm
