kicksat/Mechanical/Avionics/Main Antenna/Docked Antenna Bottom.SLDPRT

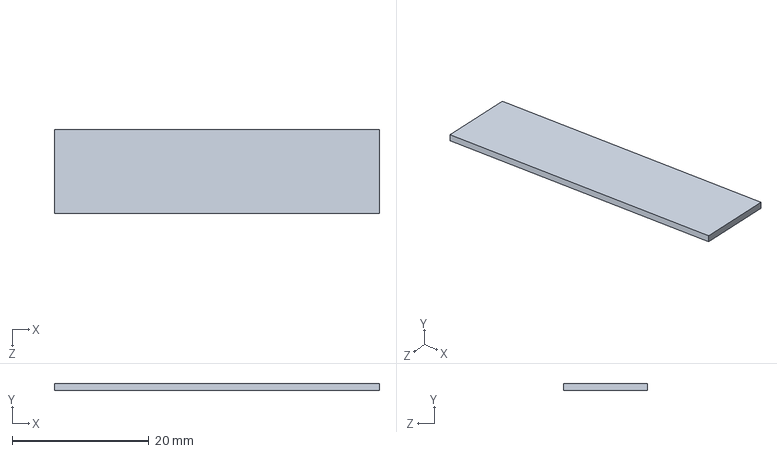
[picture p66: CAD file, 2015-09-18]
Avionics/Main Antenna/Docked Antenna Bottom.SLDPRT
47.5 x 1.00 x 12.3 mm
