kicksat/Mechanical/Mechanical & Structural Components/Bottom/DeployerSwitchExtensionPin.SLDPRT

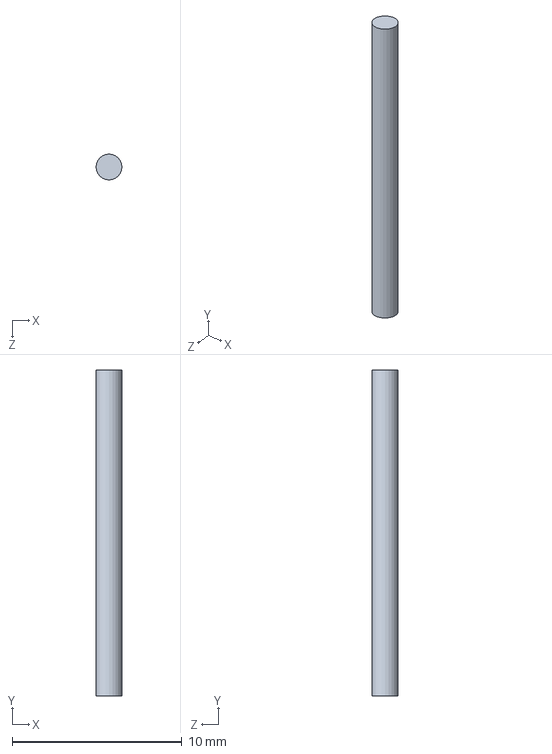
[picture p67: CAD file, 2015-09-18]
Mechanical & Structural Components/Bottom/DeployerSwitchExtensionPin.SLDPRT
1.52 x 19.2 x 1.52 mm
