kicksat/Mechanical/Mechanical & Structural Components/Sprite Housing/3dppart2.SLDPRT

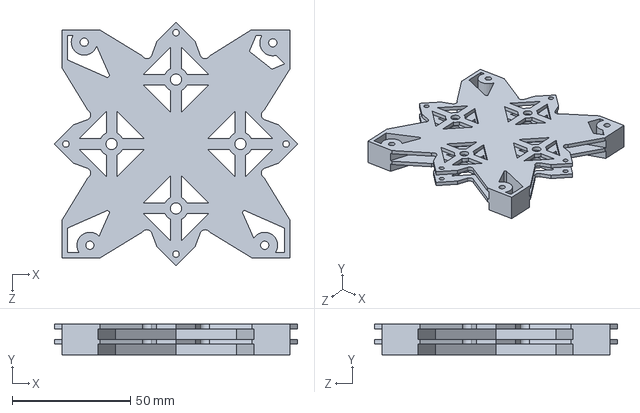
[picture p68: CAD file, 2016-02-05]
Mechanical & Structural Components/Sprite Housing/3dppart2.SLDPRT
102.6 x 13.0 x 102.6 mm
