kicksat/Mechanical/Mechanical & Structural Components/Updated Deployer/CoverPlate.SLDPRT

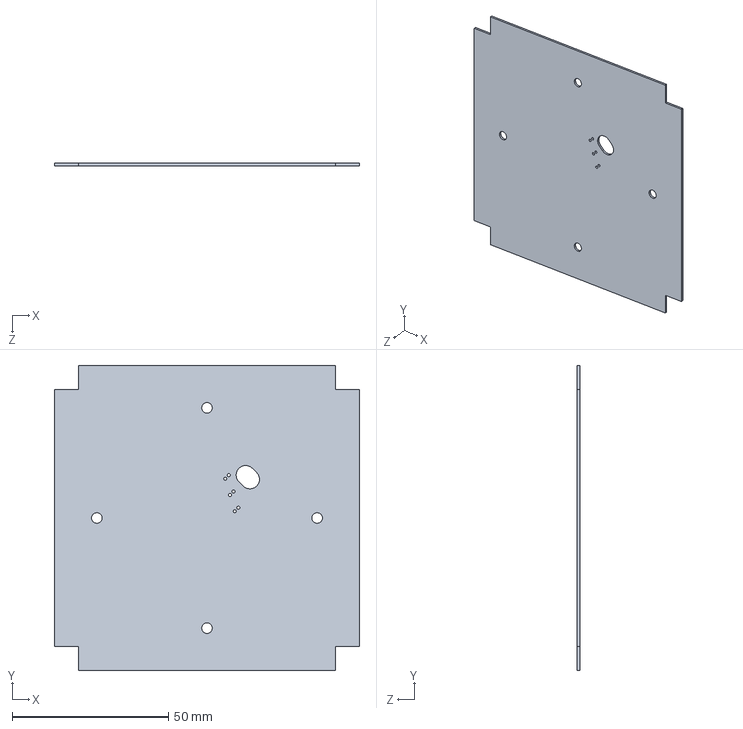
[picture p69: CAD file, 2018-08-20]
Mechanical & Structural Components/Updated Deployer/CoverPlate.SLDPRT
97.5 x 97.5 x 0.8 mm
