kicksat/Mechanical/Avionics/GPS/piksi_v2_3_cad/Patch Ant GP.1575.25.4.A.02.SLDPRT

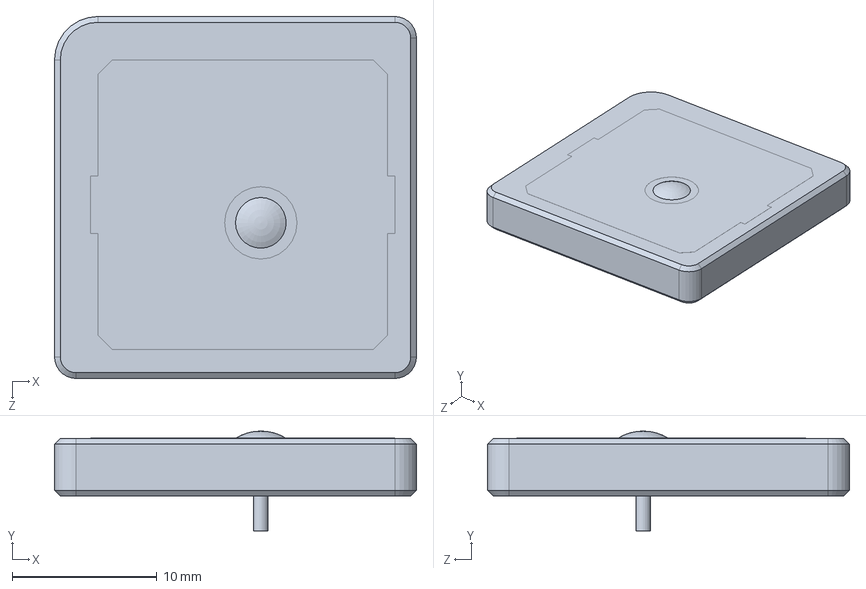
[picture p70: CAD file, 2018-08-01]
Avionics/GPS/piksi_v2_3_cad/Patch Ant GP.1575.25.4.A.02.SLDPRT
25.0 x 6.90 x 25.0 mm
