kicksat/Mechanical/Avionics/Main Antenna/Docked Antenna Side.SLDPRT

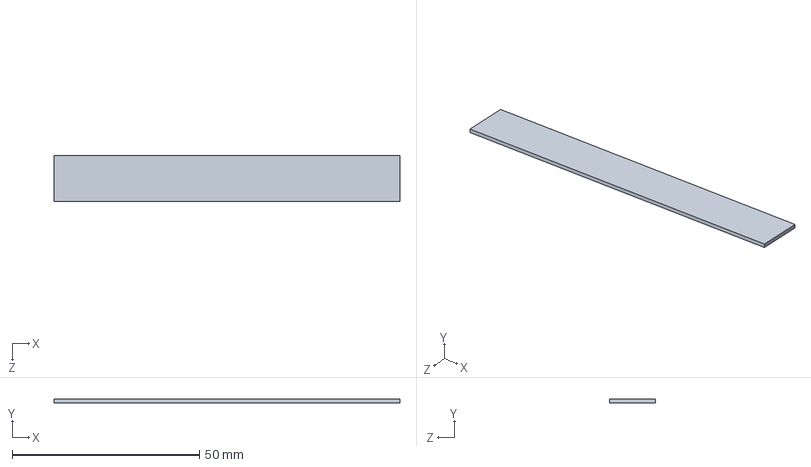
[picture p71: CAD file, 2015-09-18]
Avionics/Main Antenna/Docked Antenna Side.SLDPRT
92.5 x 1.00 x 12.3 mm
