kicksat/Mechanical/Avionics/Solar Panels/Solar Panel Clips.SLDPRT

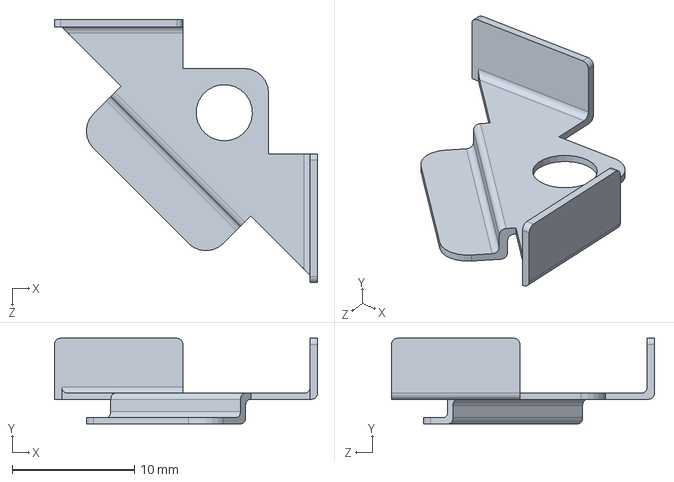
[picture p72: CAD file, 2018-08-01]
Avionics/Solar Panels/Solar Panel Clips.SLDPRT
21.5 x 7.00 x 21.5 mm
