kicksat/Mechanical/Mechanical & Structural Components/Bottom/feet.SLDPRT

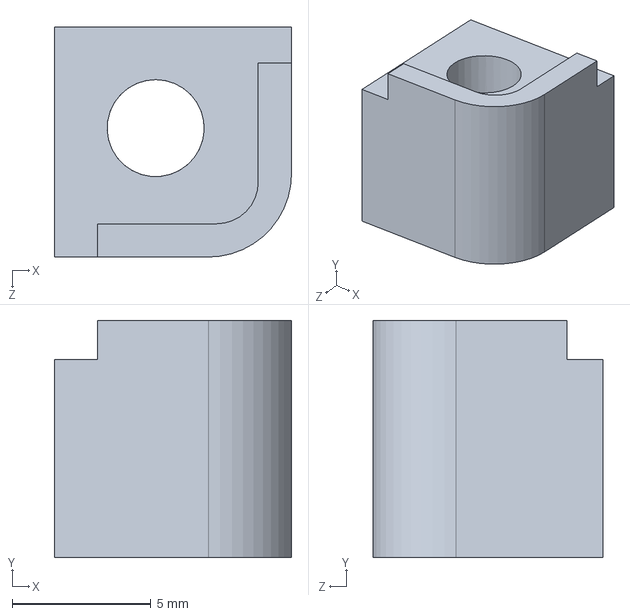
[picture p73: CAD file, 2015-09-18]
Mechanical & Structural Components/Bottom/feet.SLDPRT
8.55 x 8.55 x 8.30 mm
