kicksat/Mechanical/Mechanical & Structural Components/Sprite Deployer/BottomAntennaAttach1.SLDPRT

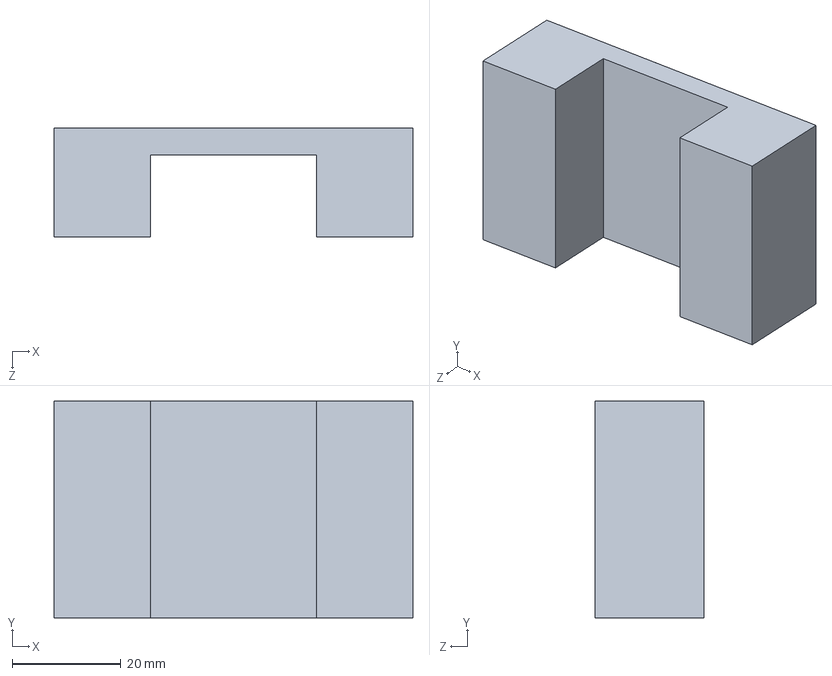
[picture p74: CAD file, 2018-08-01]
Mechanical & Structural Components/Sprite Deployer/BottomAntennaAttach1.SLDPRT
66.0 x 39.8 x 20.0 mm
