kicksat/Mechanical/Mechanical & Structural Components/Top and Deployer/Spring.SLDPRT

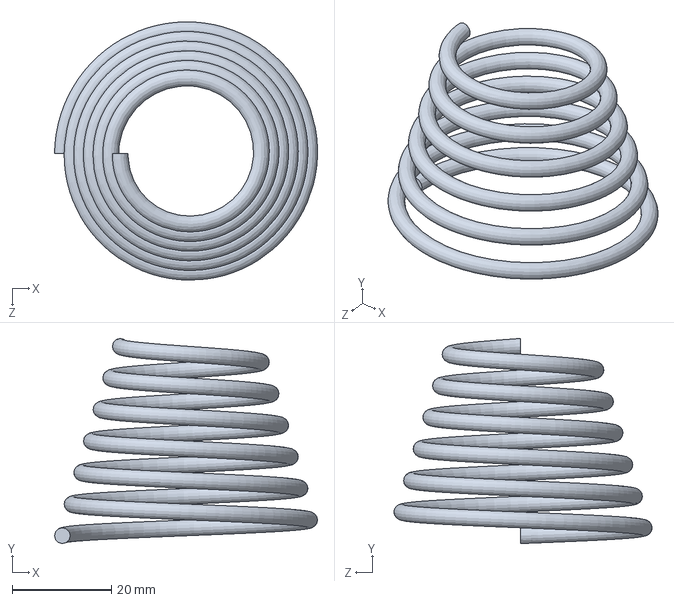
[picture p75: CAD file, 2015-09-18]
Mechanical & Structural Components/Top and Deployer/Spring.SLDPRT
52.9 x 41.3 x 52.0 mm
