kicksat/Mechanical/Mechanical & Structural Components/Updated Deployer/BottomClasp.SLDPRT

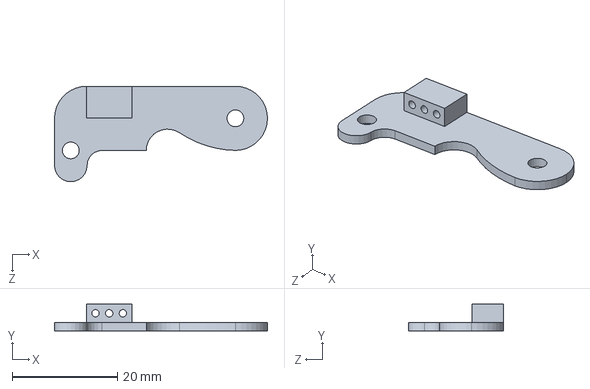
[picture p76: CAD file, 2018-08-16]
Mechanical & Structural Components/Updated Deployer/BottomClasp.SLDPRT
40.5 x 5.10 x 18.2 mm
