kicksat/Mechanical/Avionics/Batteries/battery pack cap.sldprt

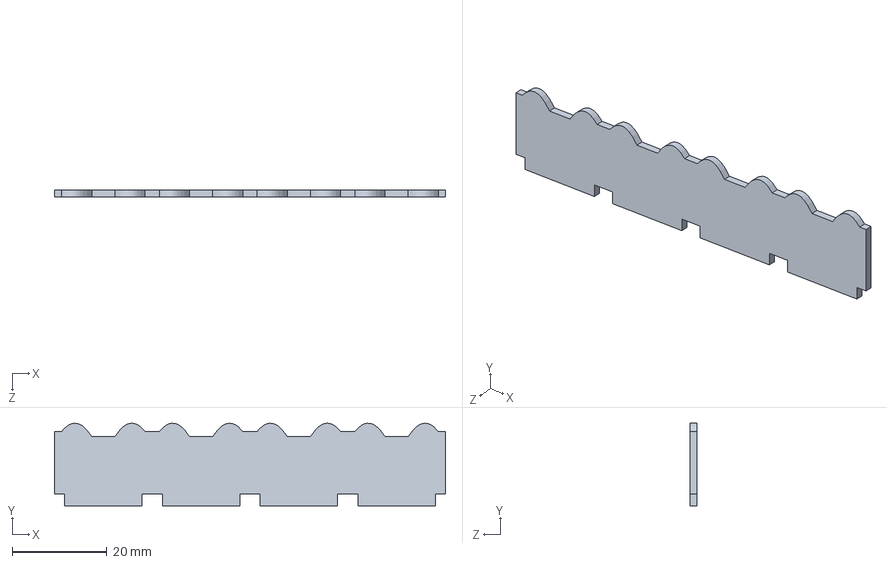
[picture p77: CAD file, 2018-08-30]
Avionics/Batteries/battery pack cap.sldprt
82.6 x 17.5 x 1.50 mm
