kicksat/Mechanical/Avionics/GPS/piksi_v2_3_cad/Can BMI-S-208-F.SLDPRT

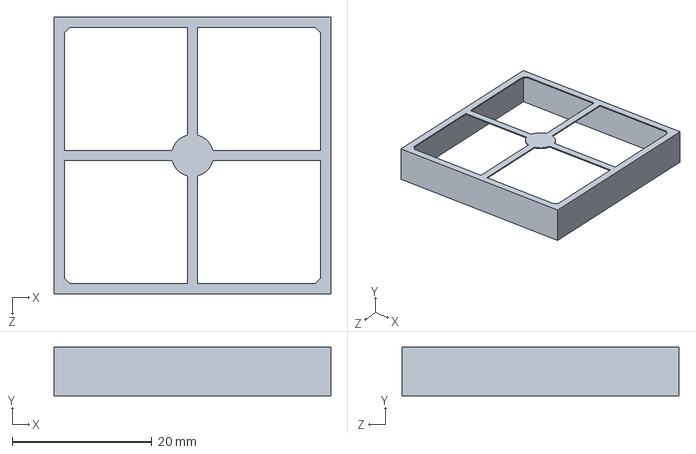
[picture p78: CAD file, 2018-08-01]
Avionics/GPS/piksi_v2_3_cad/Can BMI-S-208-F.SLDPRT
39.6 x 7.00 x 39.6 mm
