kicksat/Mechanical/Avionics/Solar Panels/Top Solar Panel.SLDPRT

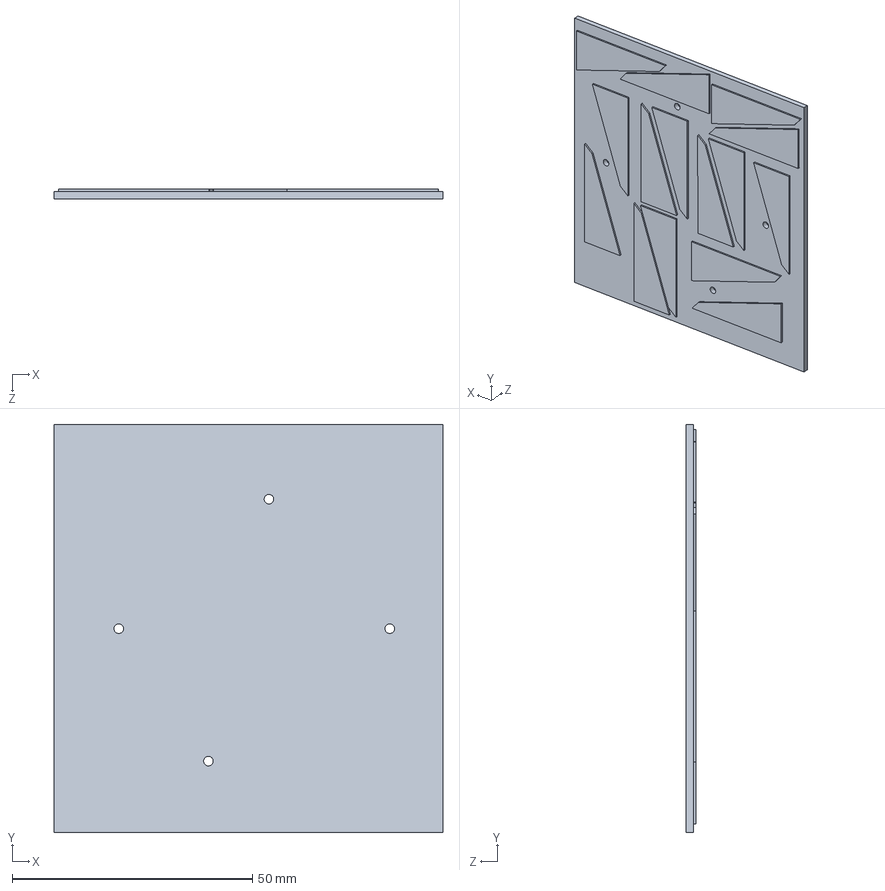
[picture p79: CAD file, 2018-08-01]
Avionics/Solar Panels/Top Solar Panel.SLDPRT
81.0 x 85.0 x 2.00 mm
