kicksat/Mechanical/Mechanical & Structural Components/Bottom/DeployerSwitchExtension.SLDPRT

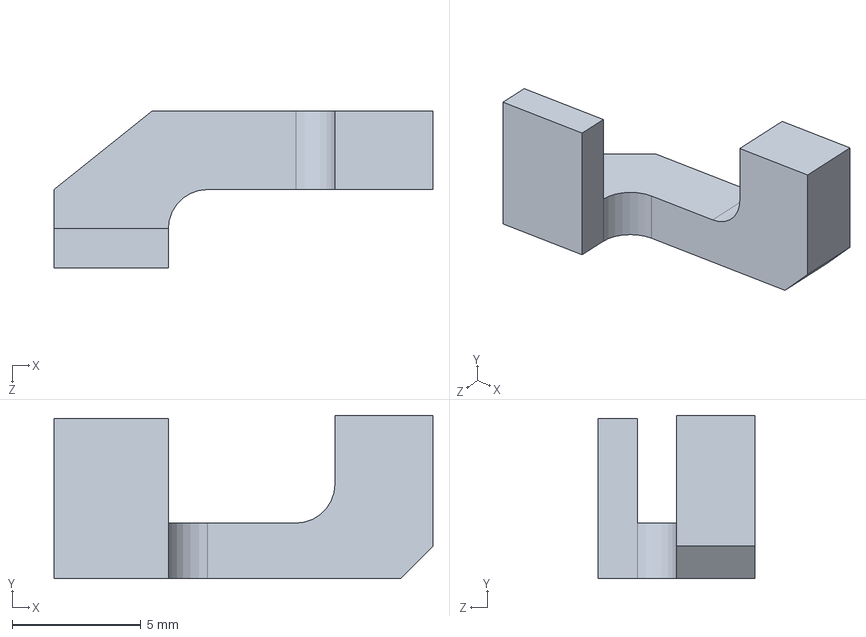
[picture p80: CAD file, 2015-09-18]
Mechanical & Structural Components/Bottom/DeployerSwitchExtension.SLDPRT
14.7 x 6.35 x 6.10 mm
