kicksat/Mechanical/Mechanical & Structural Components/Sprite Housing/Deployer Top Part.SLDPRT

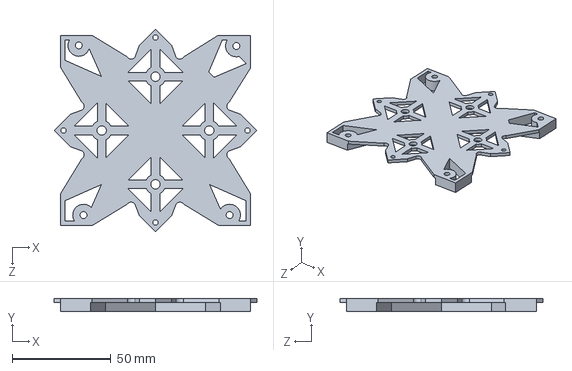
[picture p81: CAD file, 2015-12-07]
Mechanical & Structural Components/Sprite Housing/Deployer Top Part.SLDPRT
102.6 x 6.50 x 102.6 mm
