kicksat/Mechanical/Mechanical & Structural Components/Top and Deployer/Conical Spring.SLDPRT

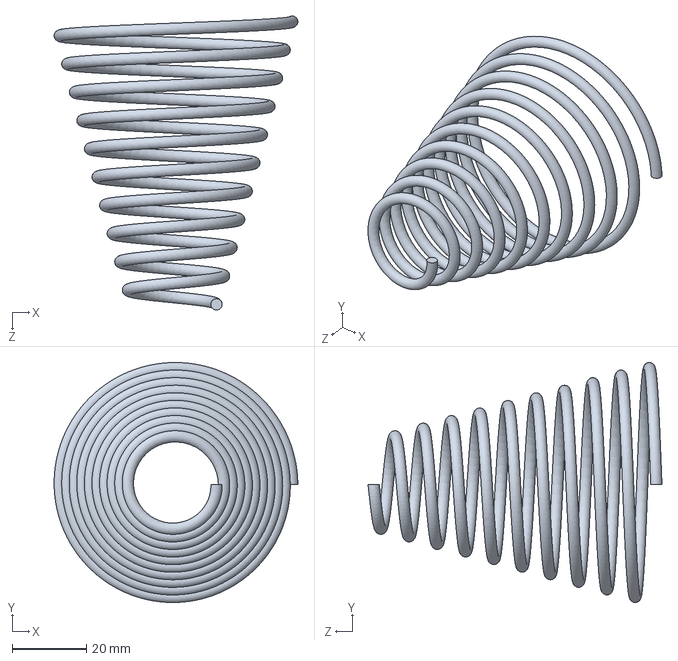
[picture p82: CAD file, 2015-09-18]
Mechanical & Structural Components/Top and Deployer/Conical Spring.SLDPRT
65.7 x 64.7 x 79.2 mm
