kicksat/Mechanical/Mechanical & Structural Components/Updated Deployer/RetentionPlate.SLDPRT

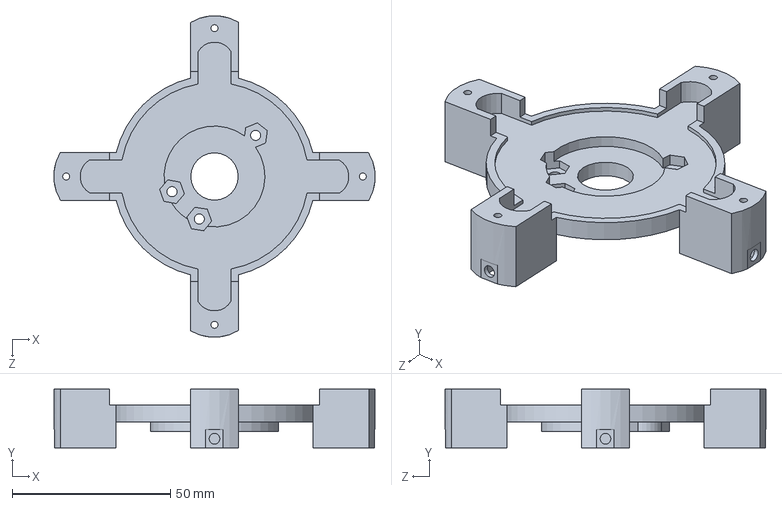
[picture p83: CAD file, 2018-08-16]
Mechanical & Structural Components/Updated Deployer/RetentionPlate.SLDPRT
101.5 x 18.6 x 101.5 mm
