kicksat/Mechanical/Avionics/GPS/piksi_v2_3_cad/T-1S15.sldprt

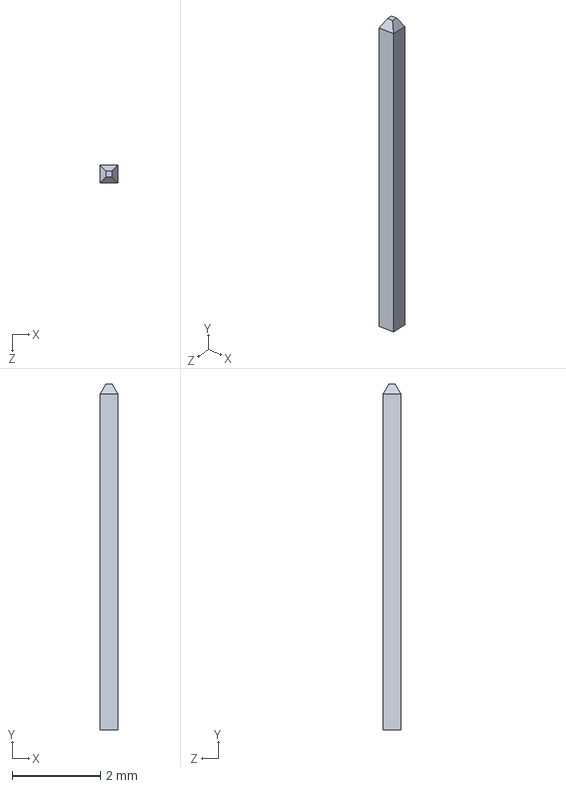
[picture p84: CAD file, 2018-08-01]
Avionics/GPS/piksi_v2_3_cad/T-1S15.sldprt
0.406 x 7.85 x 0.406 mm
