kicksat/Mechanical/Avionics/Solar Panels/Side Y Solar Cells.SLDPRT

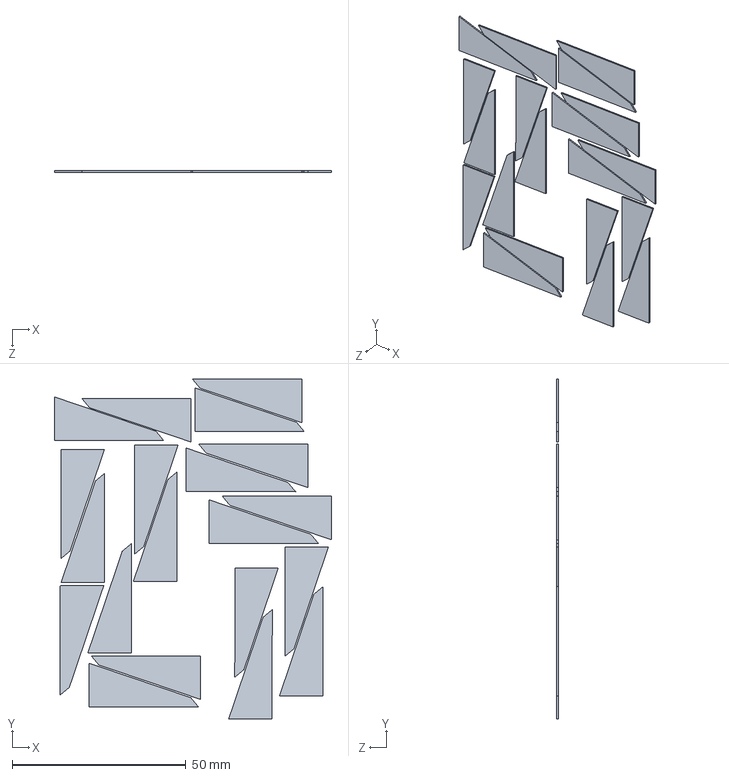
[picture p85: CAD file, 2018-08-01]
Avionics/Solar Panels/Side Y Solar Cells.SLDPRT
79.8 x 97.8 x 0.5 mm
