kicksat/Mechanical/Mechanical & Structural Components/Sprite Housing/Deployer Top Part 2.SLDPRT

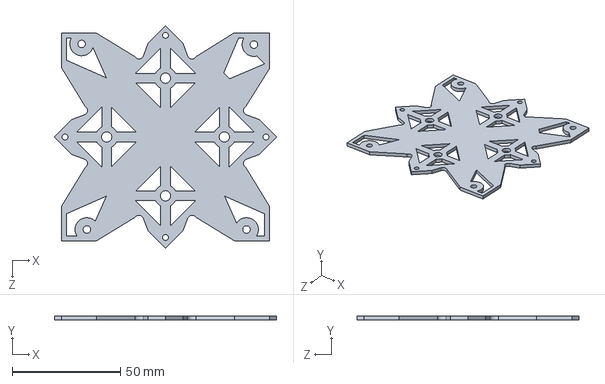
[picture p86: CAD file, 2015-12-07]
Mechanical & Structural Components/Sprite Housing/Deployer Top Part 2.SLDPRT
102.6 x 2.00 x 102.6 mm
