kicksat/Mechanical/Mechanical & Structural Components/Top and Deployer/CarbonFiberRodY.SLDPRT

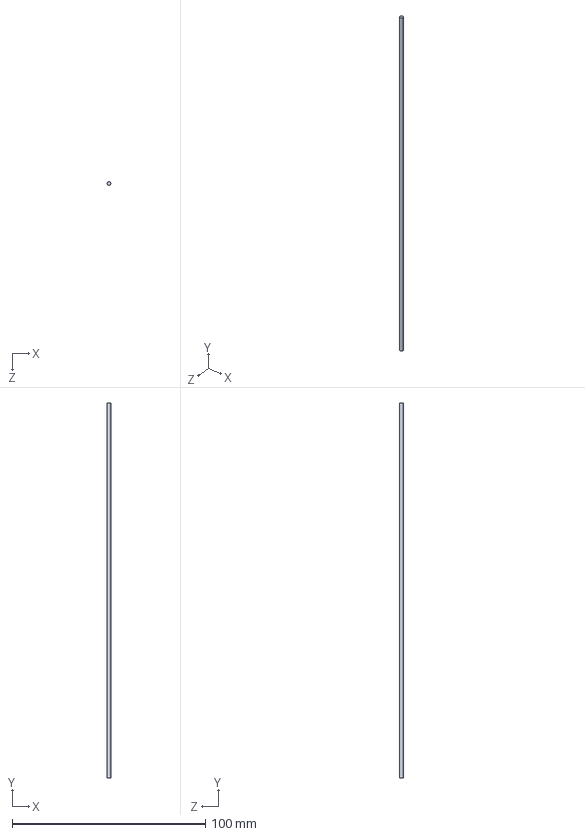
[picture p87: CAD file, 2015-09-18]
Mechanical & Structural Components/Top and Deployer/CarbonFiberRodY.SLDPRT
1.90 x 194.0 x 1.90 mm
