kicksat/Mechanical/Avionics/GPS/piksi_v2_3_cad/Molex SMA 73251-1150.SLDPRT

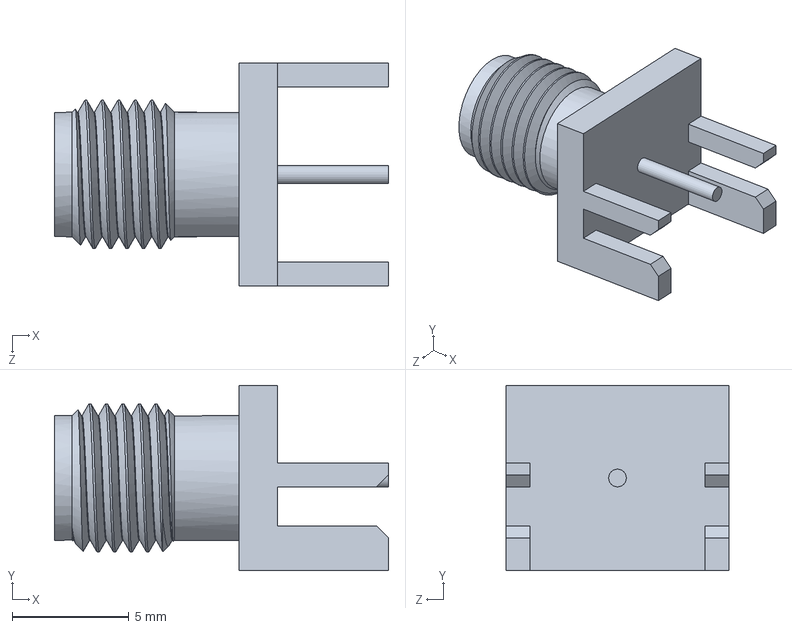
[picture p88: CAD file, 2018-08-01]
Avionics/GPS/piksi_v2_3_cad/Molex SMA 73251-1150.SLDPRT
14.3 x 7.93 x 9.53 mm
