kicksat/Mechanical/Mechanical & Structural Components/Sprite Deployer/GPSHolder.SLDPRT

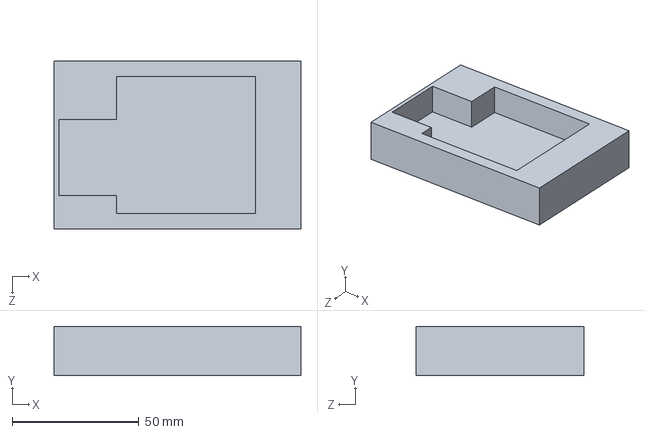
[picture p89: CAD file, 2018-08-01]
Mechanical & Structural Components/Sprite Deployer/GPSHolder.SLDPRT
97.6 x 19.5 x 66.4 mm
