kicksat/Mechanical/Mechanical & Structural Components/Sprite Housing/Base.SLDPRT

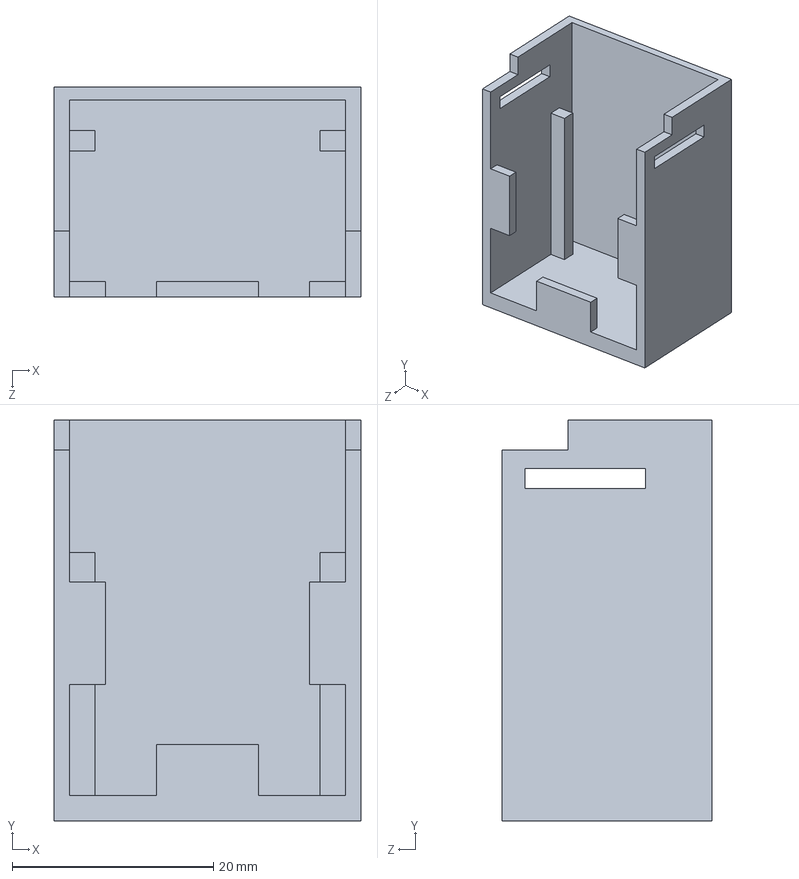
[picture p90: CAD file, 2015-12-07]
Mechanical & Structural Components/Sprite Housing/Base.SLDPRT
30.5 x 39.9 x 20.8 mm
