kicksat/Mechanical/Avionics/Batteries/M103 Battery Plate.SLDPRT

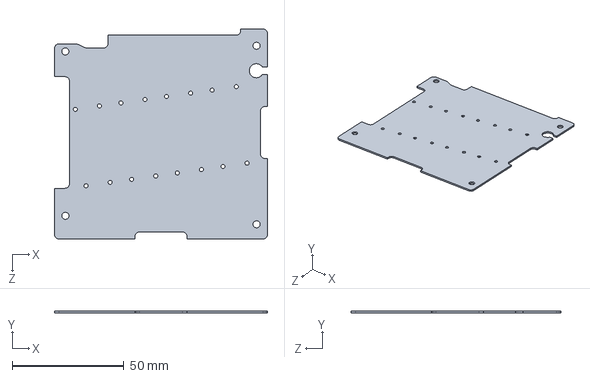
[picture p91: CAD file, 2018-08-30]
Avionics/Batteries/M103 Battery Plate.SLDPRT
95.5 x 0.9 x 94.1 mm
