kicksat/Mechanical/Avionics/Solar Panels/Top Solar Panel2.SLDPRT

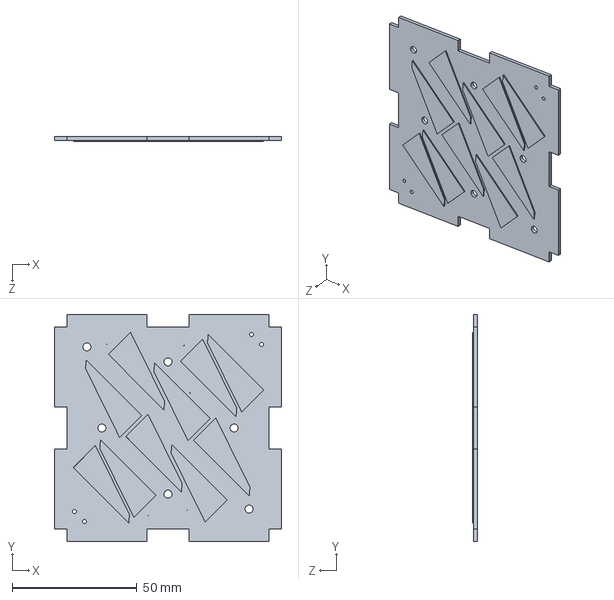
[picture p92: CAD file, 2015-10-19]
Avionics/Solar Panels/Top Solar Panel2.SLDPRT
91.0 x 91.0 x 2.01 mm
