kicksat/Mechanical/Mechanical & Structural Components/Sprite Deployer/Base.SLDPRT

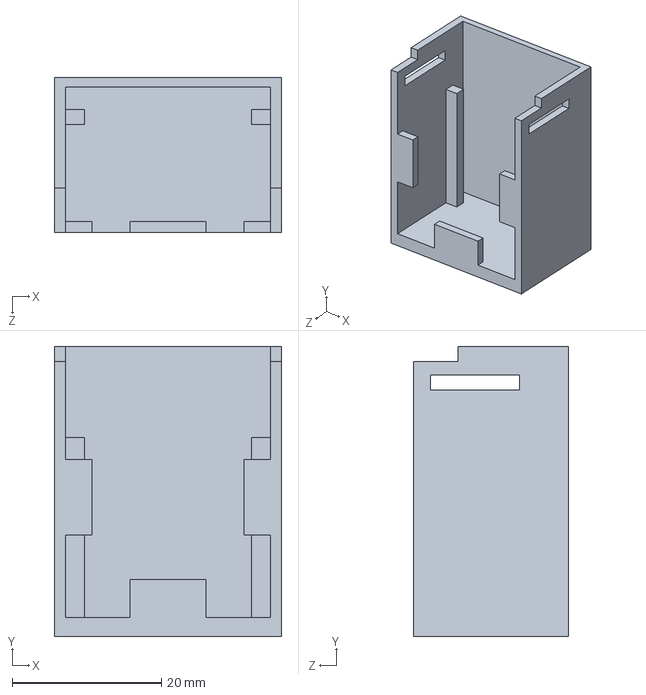
[picture p93: CAD file, 2018-08-01]
Mechanical & Structural Components/Sprite Deployer/Base.SLDPRT
30.5 x 38.9 x 20.8 mm
