kicksat/Mechanical/Mechanical & Structural Components/Sprite Housing/3dprintpart.SLDPRT

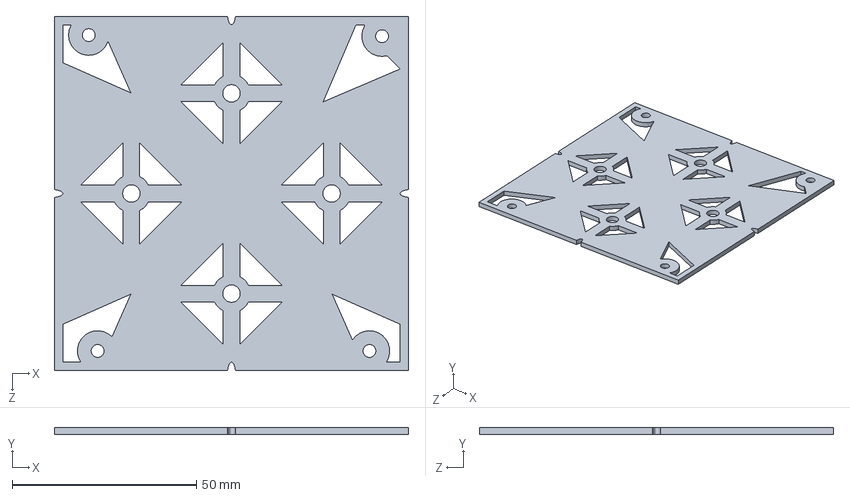
[picture p94: CAD file, 2015-12-07]
Mechanical & Structural Components/Sprite Housing/3dprintpart.SLDPRT
96.1 x 1.85 x 96.1 mm
