kicksat/Mechanical/Mechanical & Structural Components/Updated Deployer/Nut,3mm.SLDPRT

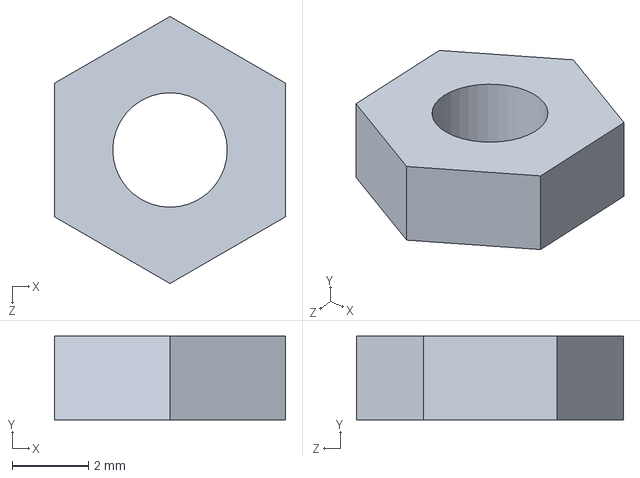
[picture p95: CAD file, 2018-07-25]
Mechanical & Structural Components/Updated Deployer/Nut,3mm.SLDPRT
6.06 x 2.20 x 7.00 mm
