kicksat/Mechanical/Avionics/Batteries/Batter Pack.SLDPRT

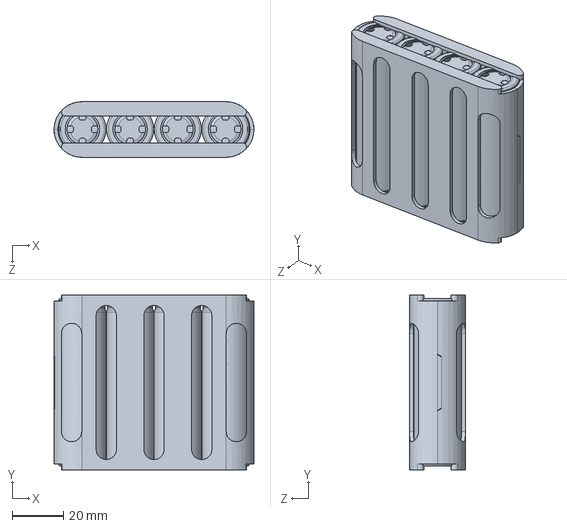
[picture p96: CAD file, 2018-08-01]
Avionics/Batteries/Batter Pack.SLDPRT
77.7 x 67.8 x 21.6 mm
