kicksat/Mechanical/Avionics/GPS/piksi_v2_3_cad/Led 0603.sldprt

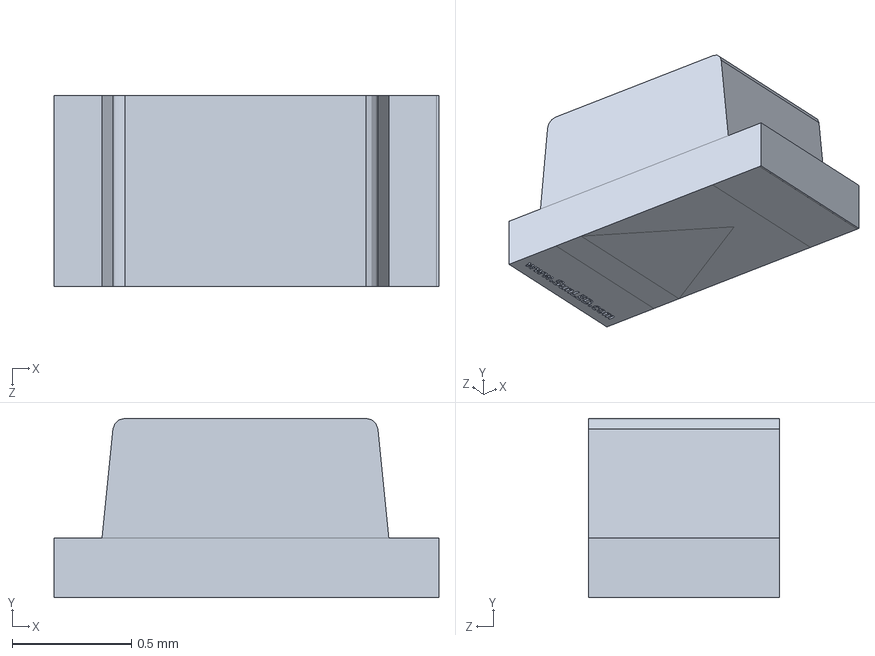
[picture p97: CAD file, 2018-08-01]
Avionics/GPS/piksi_v2_3_cad/Led 0603.sldprt
1.61 x 0.75 x 0.8 mm
