kicksat/Mechanical/Mechanical & Structural Components/Sprite Deployer/Sprites.SLDPRT

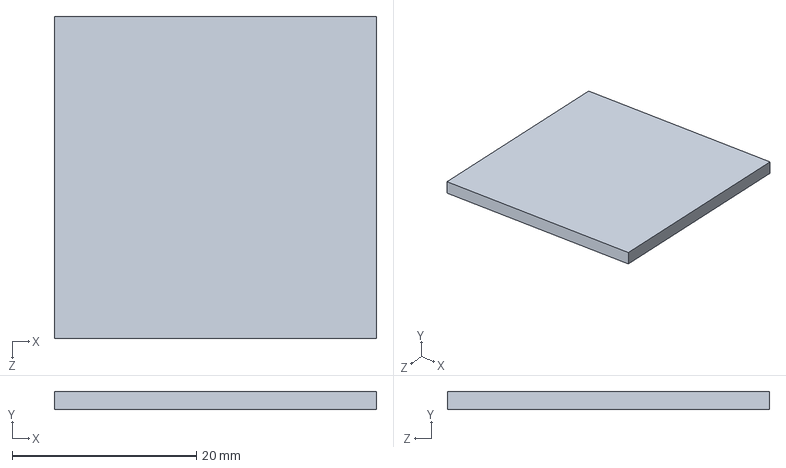
[picture p98: CAD file, 2018-08-01]
Mechanical & Structural Components/Sprite Deployer/Sprites.SLDPRT
35.0 x 2.00 x 35.0 mm
