kicksat/Mechanical/Mechanical & Structural Components/Sprite Housing/GPSHolder.SLDPRT

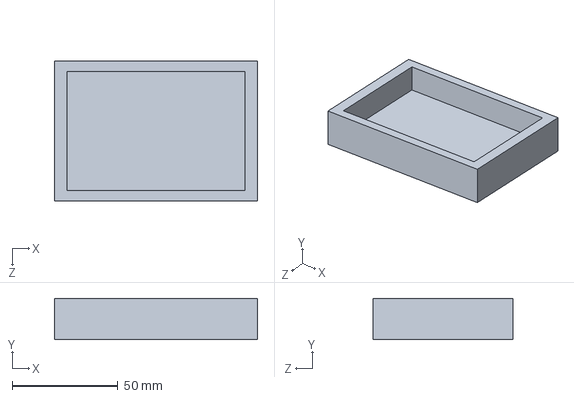
[picture p99: CAD file, 2015-12-07]
Mechanical & Structural Components/Sprite Housing/GPSHolder.SLDPRT
96.1 x 19.5 x 66.4 mm
