kicksat/Mechanical/Mechanical & Structural Components/Updated Deployer/CapNut,8mm.SLDPRT

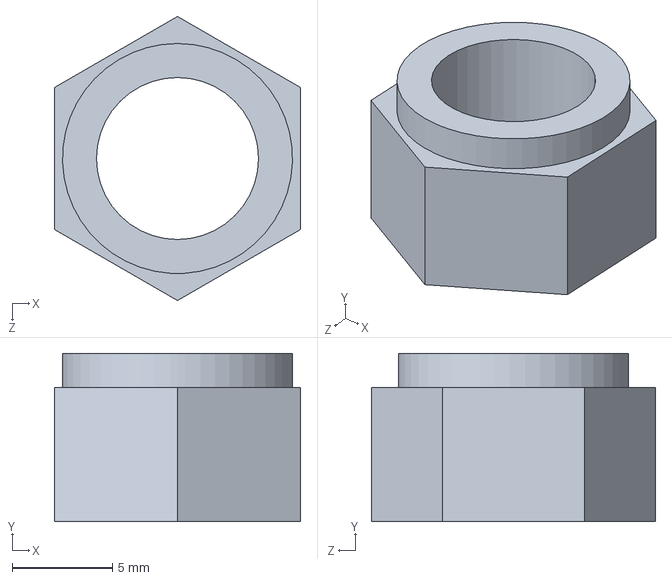
[picture p100: CAD file, 2018-07-25]
Mechanical & Structural Components/Updated Deployer/CapNut,8mm.SLDPRT
12.3 x 8.40 x 14.2 mm
