kicksat/Mechanical/Mechanical & Structural Components/Sprite Housing/Sprites.SLDPRT

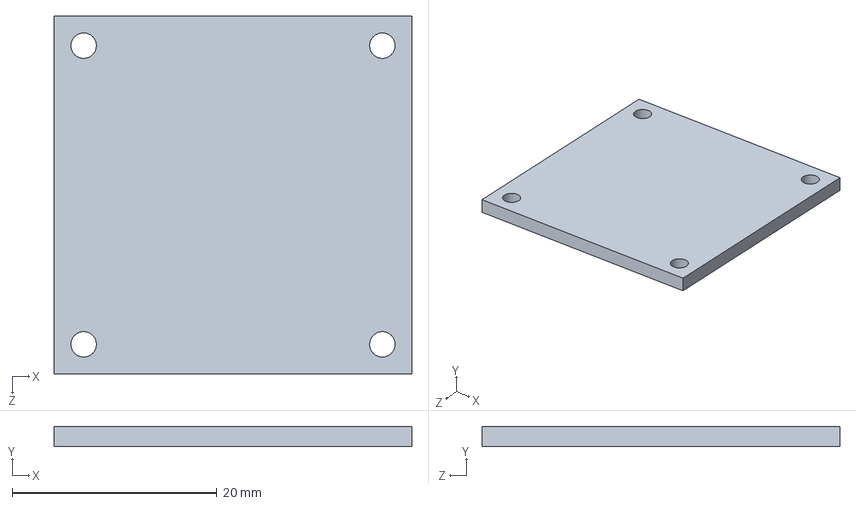
[picture p101: CAD file, 2015-11-24]
Mechanical & Structural Components/Sprite Housing/Sprites.SLDPRT
35.0 x 2.00 x 35.0 mm
