kicksat/Mechanical/Mechanical & Structural Components/Updated Deployer/Nut,8mm.SLDPRT

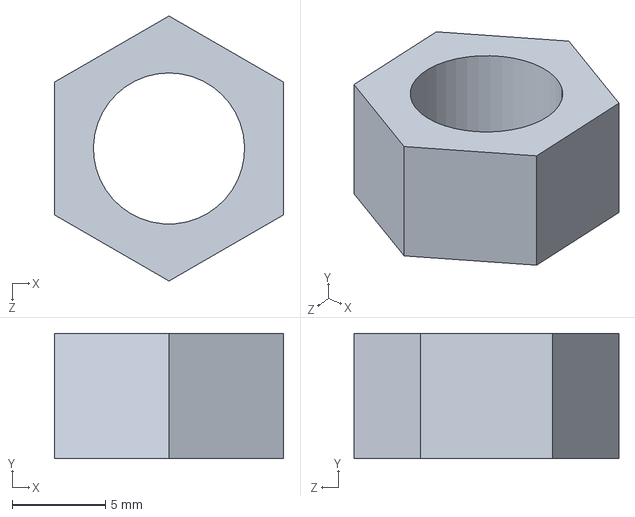
[picture p102: CAD file, 2018-07-25]
Mechanical & Structural Components/Updated Deployer/Nut,8mm.SLDPRT
12.3 x 6.70 x 14.2 mm
