kicksat/Mechanical/Mechanical & Structural Components/Sprite Housing/BottomAntennaAttach2.SLDPRT

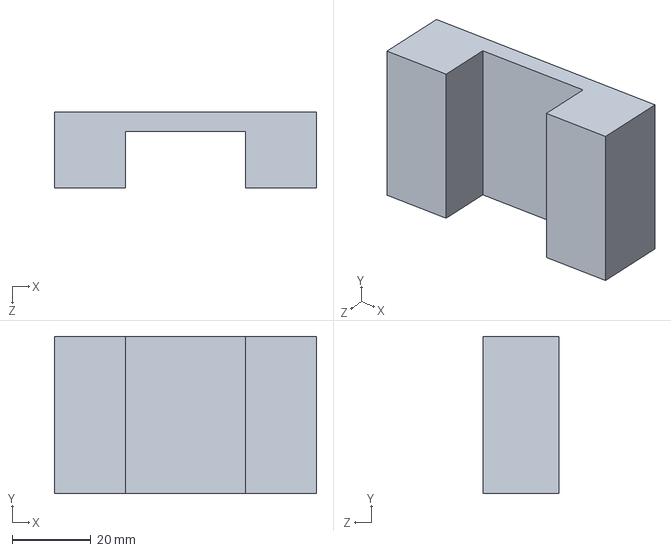
[picture p103: CAD file, 2015-11-24]
Mechanical & Structural Components/Sprite Housing/BottomAntennaAttach2.SLDPRT
66.4 x 39.8 x 19.2 mm
