kicksat/Mechanical/Mechanical & Structural Components/Sprite Housing/BottomAntennaAttach1.SLDPRT

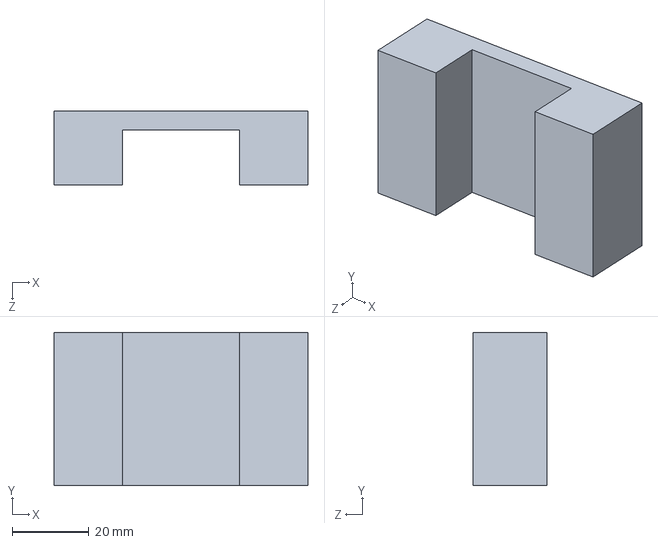
[picture p104: CAD file, 2015-11-24]
Mechanical & Structural Components/Sprite Housing/BottomAntennaAttach1.SLDPRT
66.0 x 39.8 x 19.2 mm
