kicksat/Mechanical/Avionics/Batteries/Battery Assembly.SLDASM

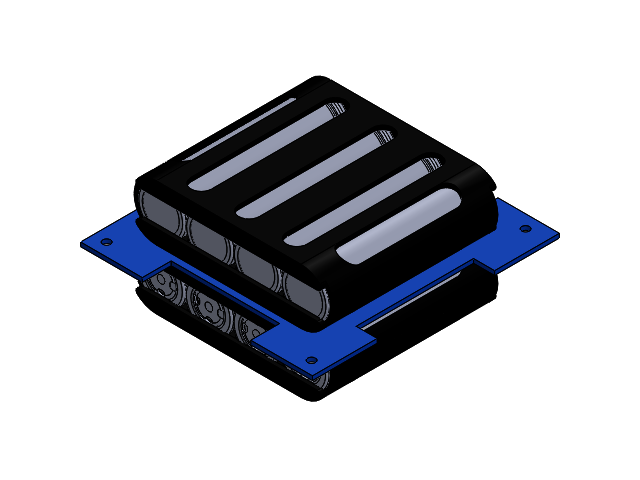
[picture p105: CAD file, 2018-08-01]
Avionics/Batteries/Battery Assembly.SLDASM
Antenna Splitter Holder
Batter Pack x 2
